FabSpi/Zone-Controller/KiCAD_libs/BC847BVN-7.step

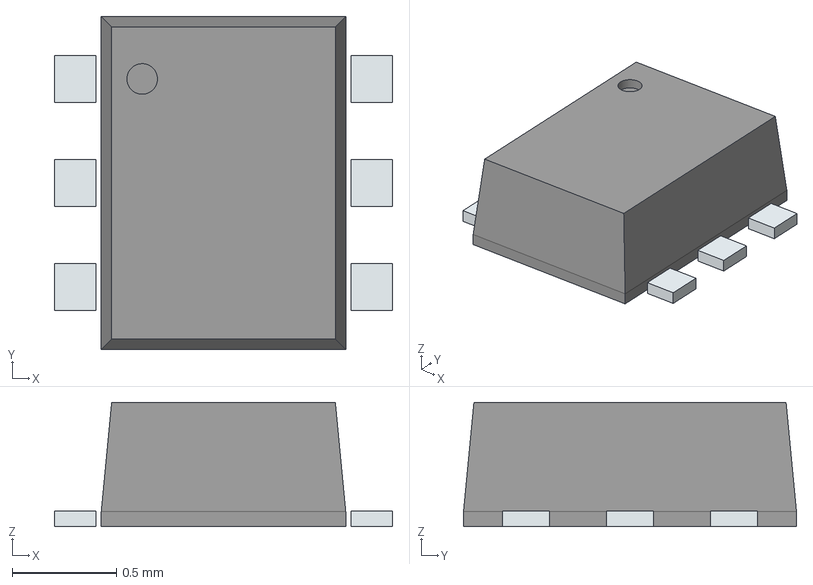
[picture p15: CAD file, 2025-10-27]
KiCAD_libs/BC847BVN-7.step
1.62 x 1.60 x 0.598 mm
PinsArrayL
PinsArrayR
