FabSpi/Zone-Controller/KiCAD_libs/TJA1022TK_118.step

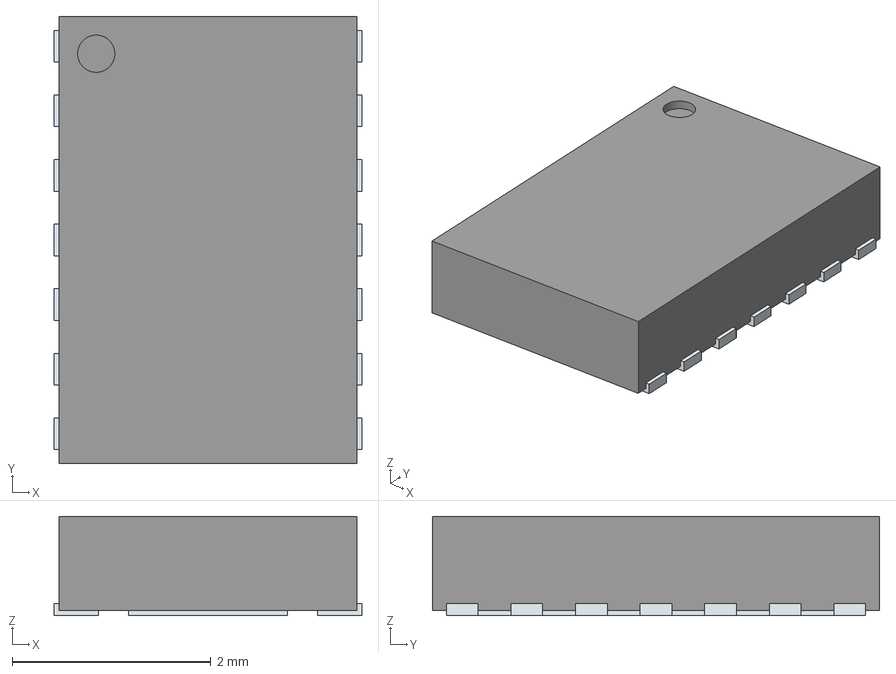
[picture p16: CAD file, 2025-10-27]
KiCAD_libs/TJA1022TK_118.step
3.10 x 4.50 x 1.00 mm
ThermalPin
PinsArrayLR
