FabSpi/Zone-Controller/KiCAD_libs/MFS2633AMBA0AD.step

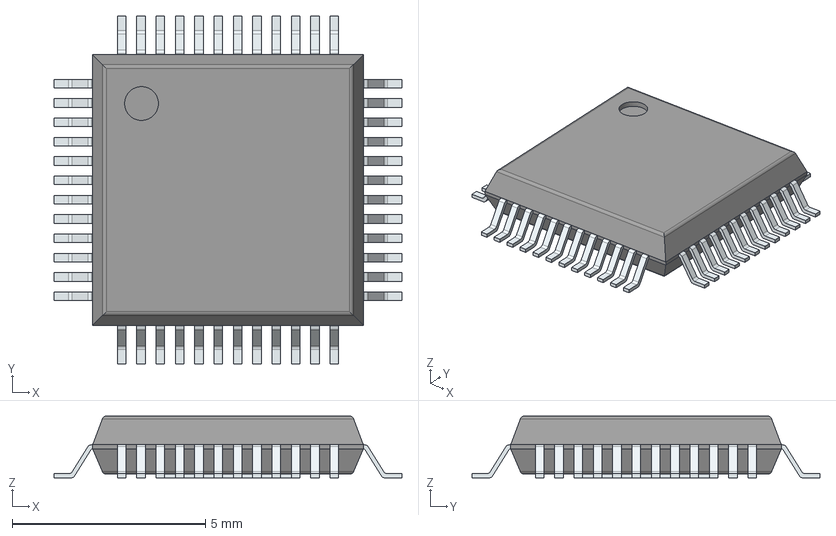
[picture p17: CAD file, 2025-10-27]
KiCAD_libs/MFS2633AMBA0AD.step
9.00 x 9.00 x 1.60 mm
PinsArrayLR
PinsArrayTB
ThermalPad
