FabSpi/Zone-Controller/KiCAD_libs/TJA1101BHN_0Z.step

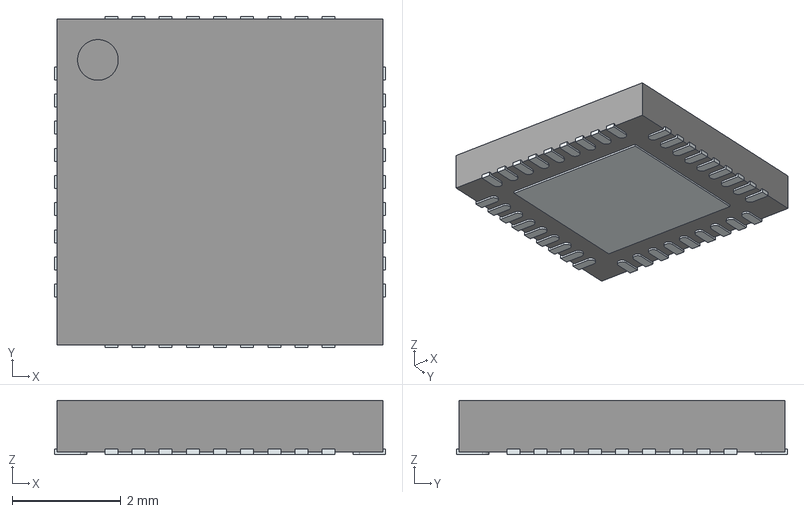
[picture p18: CAD file, 2025-10-27]
KiCAD_libs/TJA1101BHN_0Z.step
6.10 x 6.10 x 1.00 mm
ThermalPin
PinsArrayLR
PinsArrayTB
