FabSpi/Zone-Controller/KiCAD_libs/8.06.04_J-LINK_NEEDLE_ADAPTER.step

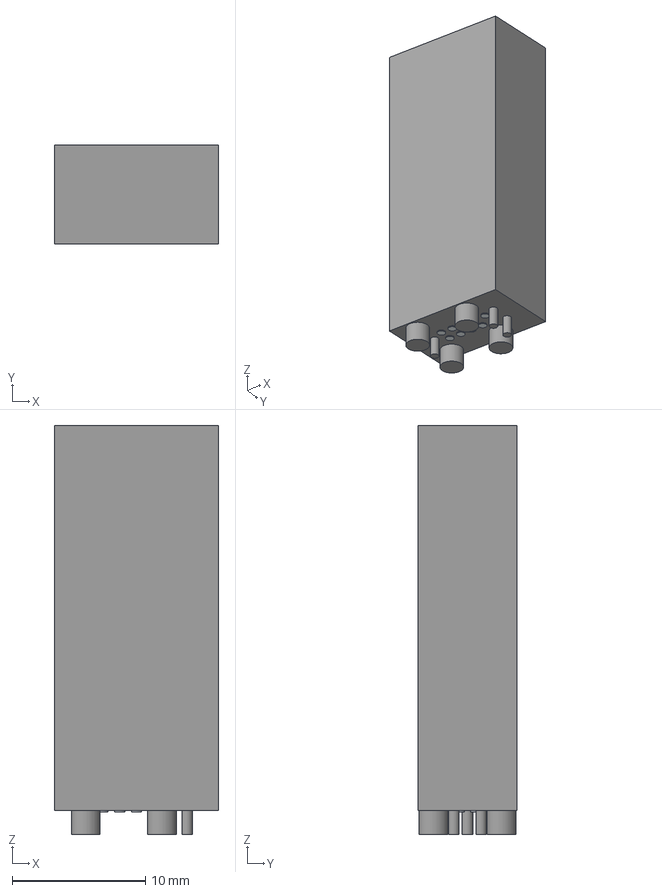
[picture p19: CAD file, 2025-10-27]
KiCAD_libs/8.06.04_J-LINK_NEEDLE_ADAPTER.step
12.3 x 7.45 x 30.7 mm
Pins
Lugs
