FabSpi/Zone-Controller/KiCAD_libs/NE555DR.step

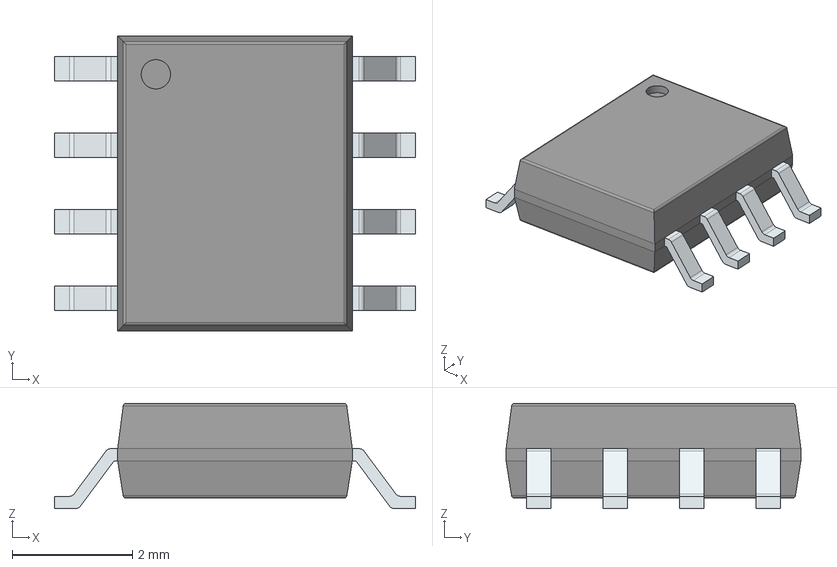
[picture p20: CAD file, 2025-10-27]
KiCAD_libs/NE555DR.step
6.00 x 4.90 x 1.75 mm
PinsArrayLR
