FabSpi/Zone-Controller/KiCAD_libs/MPLC0730L4R7.step

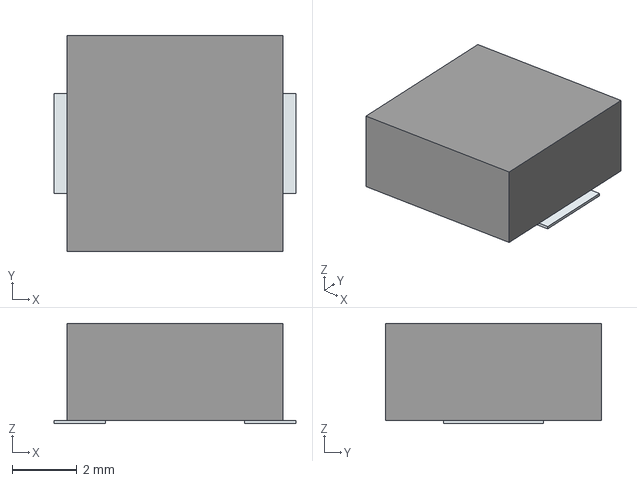
[picture p21: CAD file, 2025-10-27]
KiCAD_libs/MPLC0730L4R7.step
7.50 x 6.70 x 3.10 mm
Pins
