FabSpi/Zone-Controller/Zonencontroller/Zonencontroller.kicad_sch

## KiCad design Zonencontroller/Zonencontroller.kicad_sch (2025-10-27)

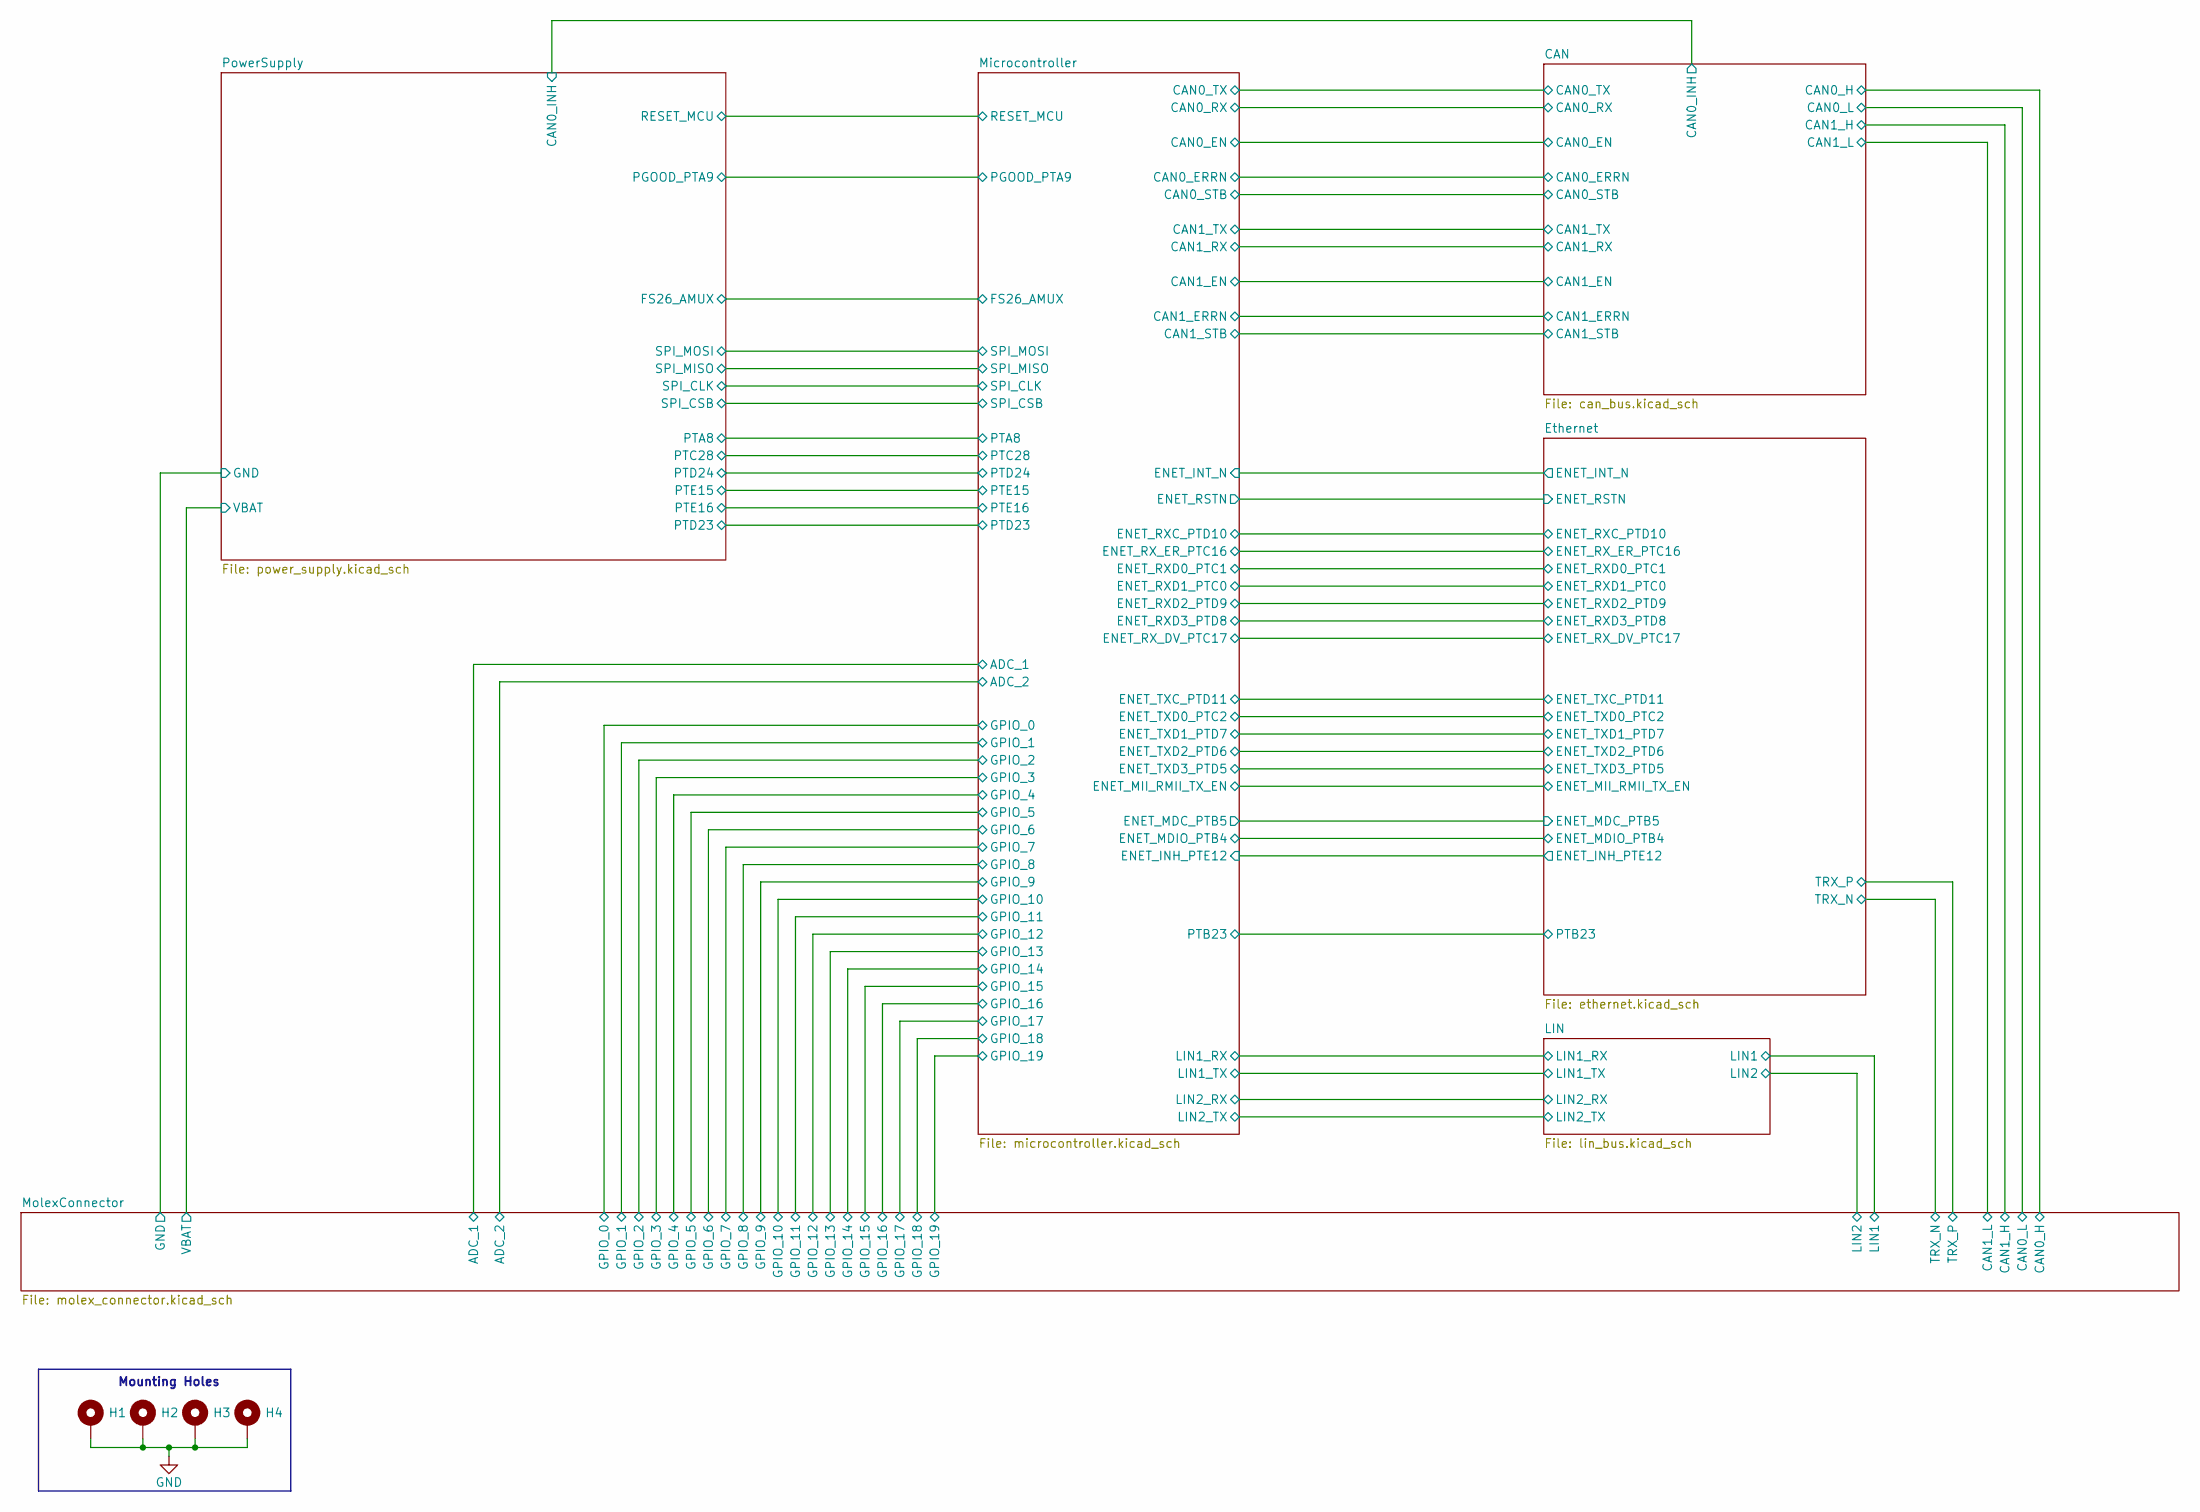
[picture p23: schematic Zonencontroller.kicad_sch]

Parts:
H1, H2, H3, H4: MountingHole_Pad; MountingHole_4.3mm_M4_DIN965_Pad_TopBottom

Connections:
GND: H1.1, H2.1, H3.1, H4.1

Notes on the sheet:
Mounting Holes
