FabSpi/Zone-Controller/Zonencontroller/can_bus.kicad_sch

## KiCad design Zonencontroller/can_bus.kicad_sch (2025-10-27)

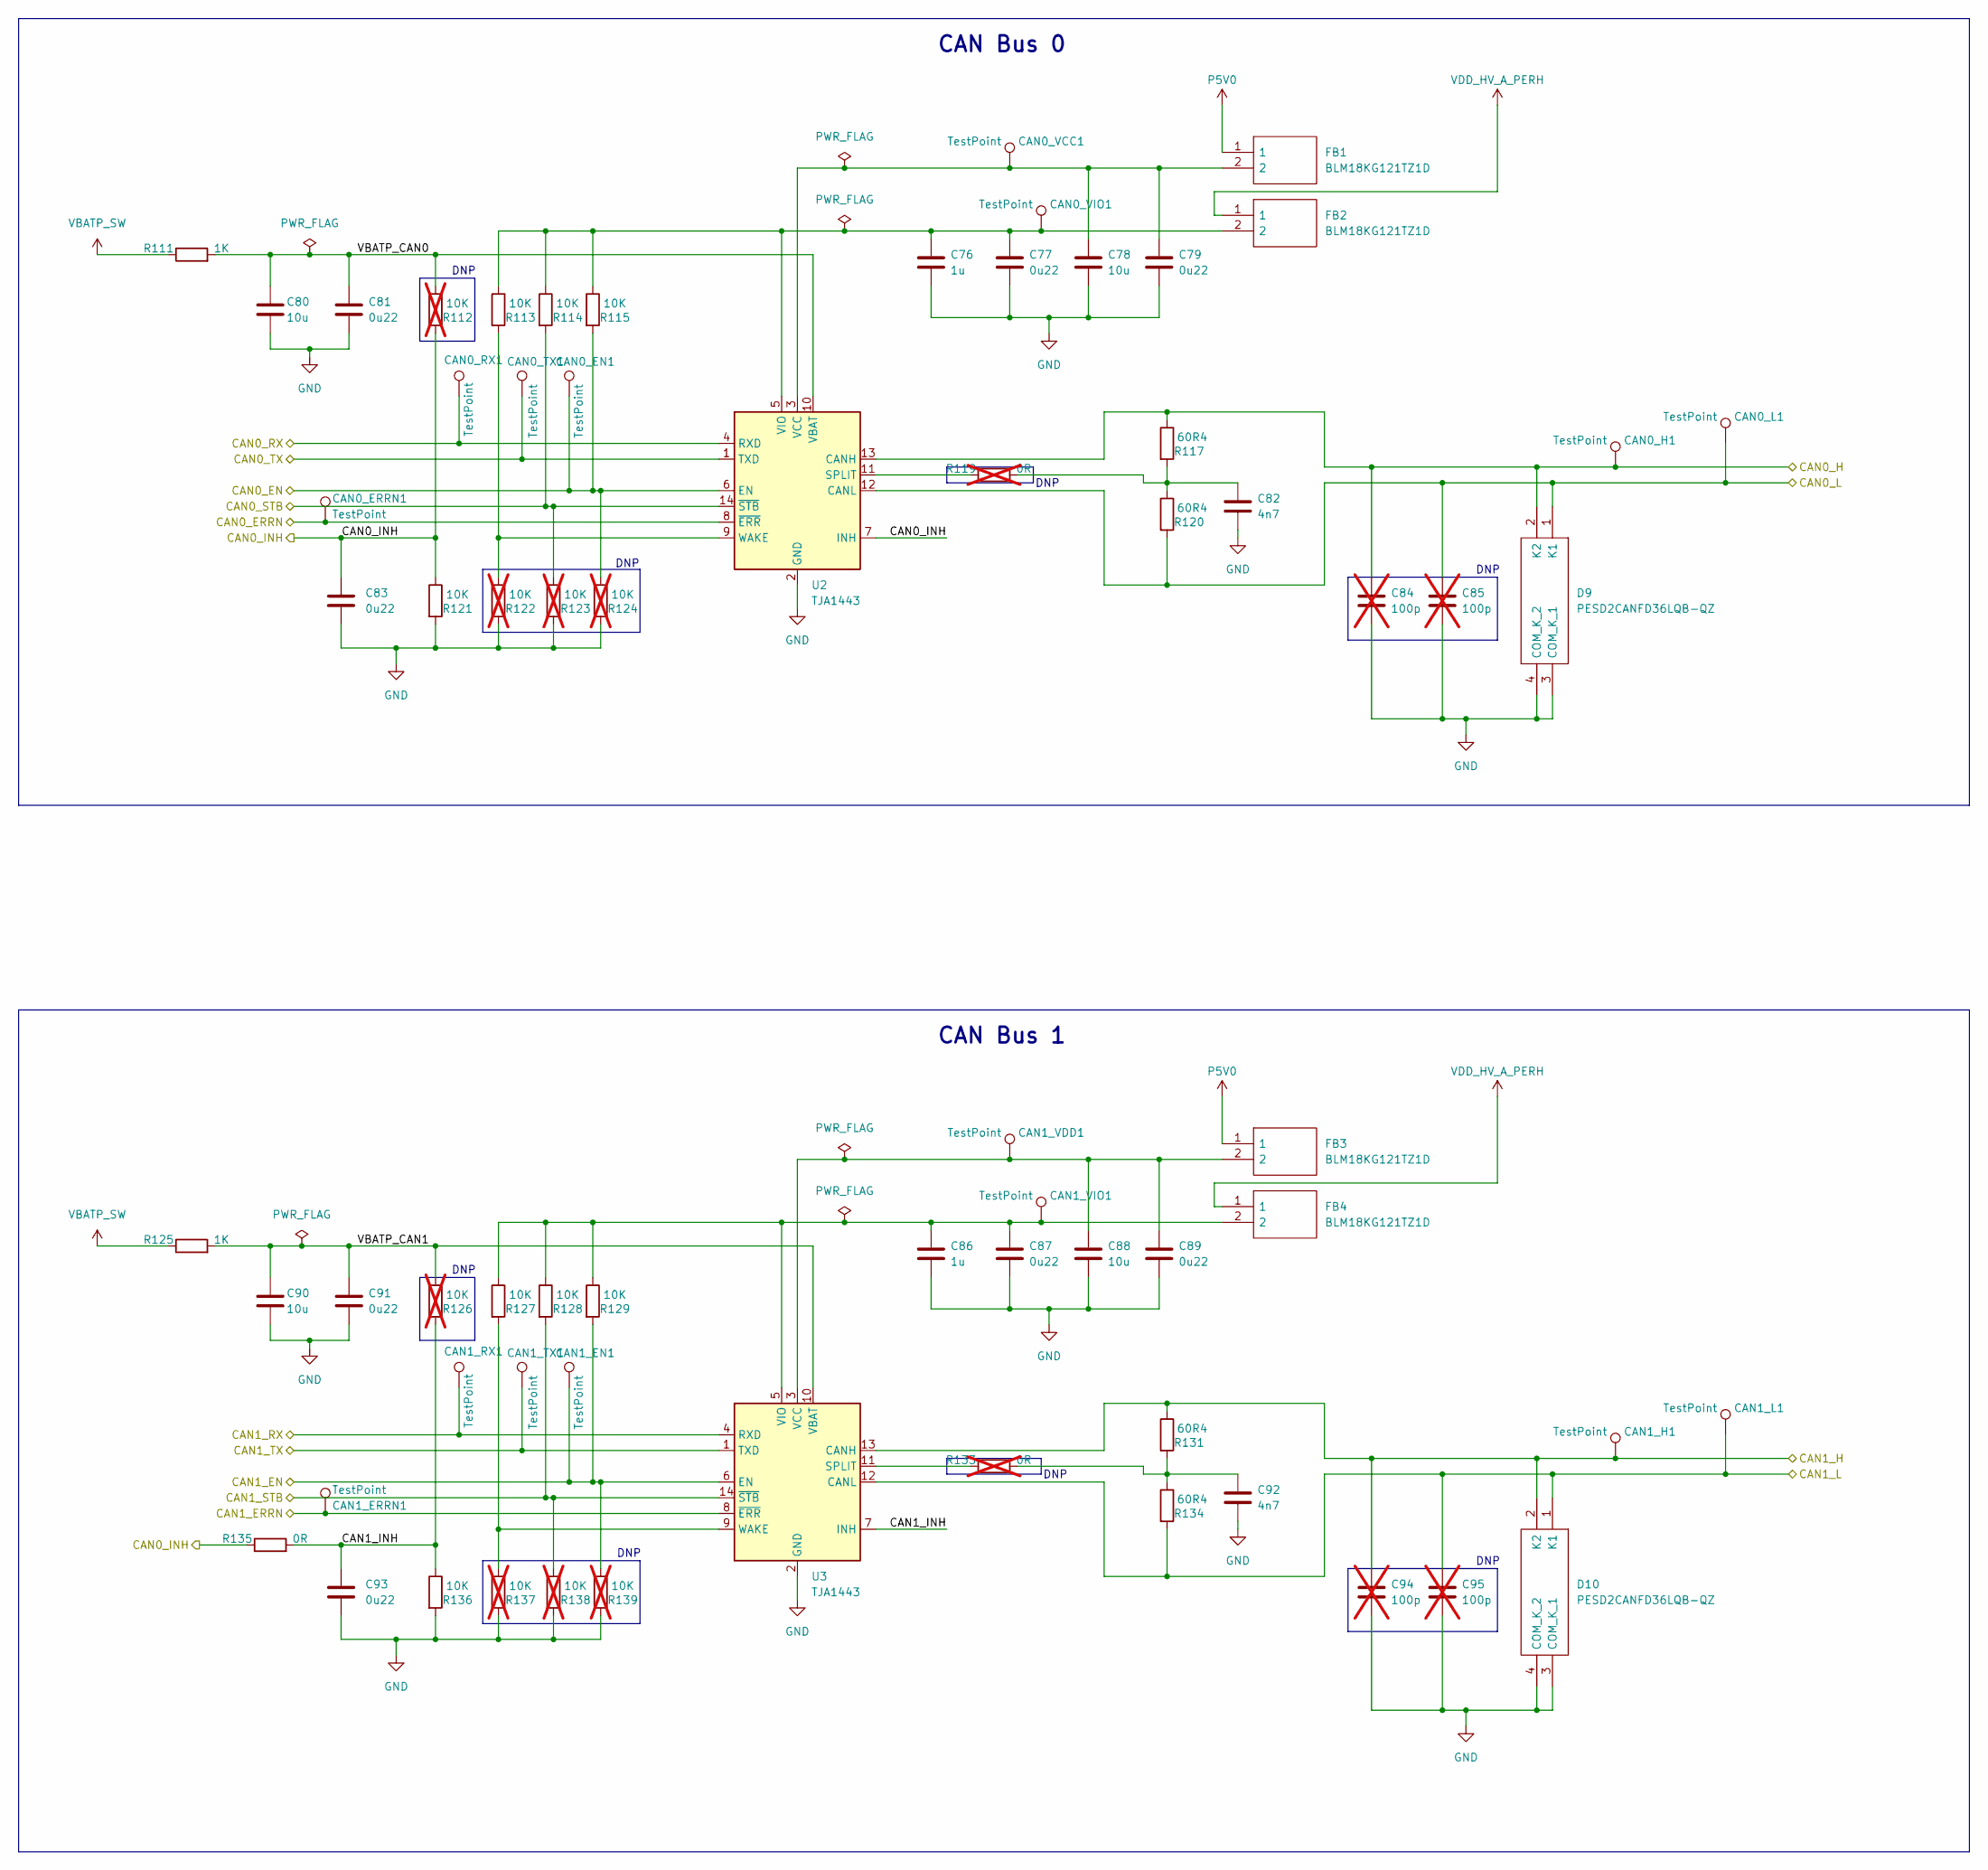
[picture p24: schematic can_bus.kicad_sch]

Parts:
C76, C86: 1u; C_0603_1608Metric
C77, C79, C81, C83, C87, C89, C91, C93: 0u22; C_0603_1608Metric
C78, C80, C88, C90: 10u; C_1206_3216Metric
C82, C92: 4n7; C_0603_1608Metric
C84, C85, C94, C95: 100p; C_0603_1608Metric; not fitted
CAN0_EN1, CAN0_ERRN1, CAN0_H1, CAN0_L1, CAN0_RX1, CAN0_TX1, CAN0_VCC1, CAN0_VIO1, CAN1_EN1, CAN1_ERRN1, CAN1_H1, CAN1_L1, CAN1_RX1, CAN1_TX1, CAN1_VDD1, CAN1_VIO1: TestPoint; TestPoint_Pad_D2.0mm
D9, D10: PESD2CANFD36LQB-QZ; PESD2CANFD36LQBQZ; Manufacturer_Part_Number PESD2CANFD36LQB-QZ; Mouser Part Number 771-PESD2CANFD3LQBQZ
FB1, FB2, FB3, FB4: BLM18KG121TZ1D; BLM18EG101TH1D; Manufacturer_Part_Number BLM18KG121TZ1D; Mouser Part Number 81-BLM18KG121TZ1D
R111, R125: 1K; R_0603_1608Metric
R112, R122, R123, R124, R126, R137, R138, R139: 10K; R_0603_1608Metric; not fitted
R113, R114, R115, R121, R127, R128, R129, R136: 10K; R_0603_1608Metric
R117, R120, R131, R134: 60R4; R_0603_1608Metric
R119, R133: 0R; R_0603_1608Metric; not fitted
R135: 0R; SolderJumper-2_P1.3mm_Bridged_Pad1.0x1.5mm
U2, U3: TJA1443; SOIC-14_3.9x8.7mm_P1.27mm

Connections:
CAN0_EN: CAN0_EN1.1, R115.2, R124.1, U2.6 (EN)
CAN0_ERRN: CAN0_ERRN1.1, U2.8 (~ERR)
CAN0_H: C84.1, CAN0_H1.1, D9.2 (K2), R117.1, U2.13 (CANH)
CAN0_INH: C83.1, R112.2, R121.1, R135.1, U2.7 (INH)
CAN0_L: C85.1, CAN0_L1.1, D9.1 (K1), R120.2, U2.12 (CANL)
CAN0_RX: CAN0_RX1.1, U2.4 (RXD)
CAN0_STB: R114.2, R123.1, U2.14 (~STB)
CAN0_TX: CAN0_TX1.1, U2.1 (TXD)
CAN1_EN: CAN1_EN1.1, R129.2, R139.1, U3.6 (EN)
CAN1_ERRN: CAN1_ERRN1.1, U3.8 (~ERR)
CAN1_H: C94.1, CAN1_H1.1, D10.2 (K2), R131.1, U3.13 (CANH)
CAN1_INH: C93.1, R126.2, R135.2, R136.1, U3.7 (INH)
CAN1_L: C95.1, CAN1_L1.1, D10.1 (K1), R134.2, U3.12 (CANL)
CAN1_RX: CAN1_RX1.1, U3.4 (RXD)
CAN1_STB: R128.2, R138.1, U3.14 (~STB)
CAN1_TX: CAN1_TX1.1, U3.1 (TXD)
GND: C76.2, C77.2, C78.2, C79.2, C80.2, C81.2, C82.2, C83.2, C84.2, C85.2, C86.2, C87.2, C88.2, C89.2, C90.2, C91.2, C92.2, C93.2, C94.2, C95.2, D9.3 (COM_K_1), D9.4 (COM_K_2), D10.3 (COM_K_1), D10.4 (COM_K_2), R121.2, R122.2, R123.2, R124.2, R136.2, R137.2, R138.2, R139.2, U2.2 (GND), U3.2 (GND)
unnamed: C76.1, C77.1, CAN0_VIO1.1, FB2.2, R113.1, R114.1, R115.1, U2.5 (VIO)
unnamed: C78.1, C79.1, CAN0_VCC1.1, FB1.2, U2.3 (VCC)
unnamed: C82.1, R117.2, R119.2, R120.1
unnamed: C86.1, C87.1, CAN1_VIO1.1, FB4.2, R127.1, R128.1, R129.1, U3.5 (VIO)
unnamed: C88.1, C89.1, CAN1_VDD1.1, FB3.2, U3.3 (VCC)
unnamed: C92.1, R131.2, R133.2, R134.1
unnamed: R113.2, R122.1, U2.9 (WAKE)
unnamed: R119.1, U2.11 (SPLIT)
unnamed: R127.2, R137.1, U3.9 (WAKE)
unnamed: R133.1, U3.11 (SPLIT)
P5V0: FB1.1, FB3.1
VBATP_CAN0: C80.1, C81.1, R111.2, R112.1, U2.10 (VBAT)
VBATP_CAN1: C90.1, C91.1, R125.2, R126.1, U3.10 (VBAT)
VBATP_SW: R111.1, R125.1
VDD_HV_A_PERH: FB2.1, FB4.1

Notes on the sheet:
DNP
CAN Bus 0
CAN Bus 1
