FabSpi/Zone-Controller/Zonencontroller/ethernet.kicad_sch

## KiCad design Zonencontroller/ethernet.kicad_sch (2025-10-27)

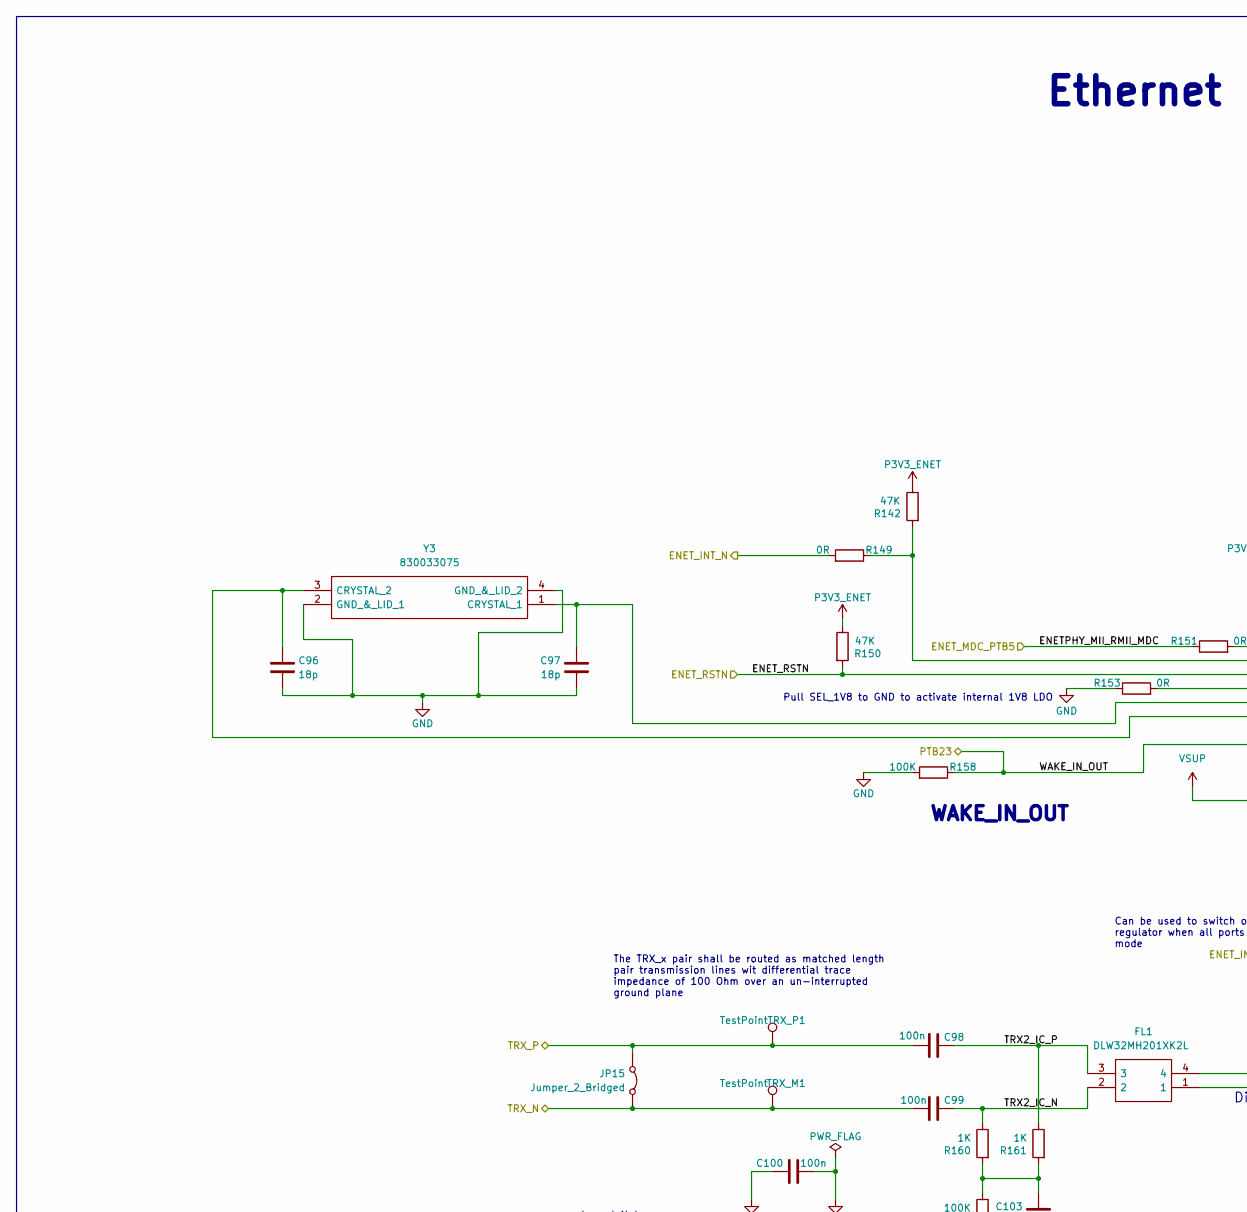
[picture p25: schematic ethernet.kicad_sch, part in row 1, column 1]

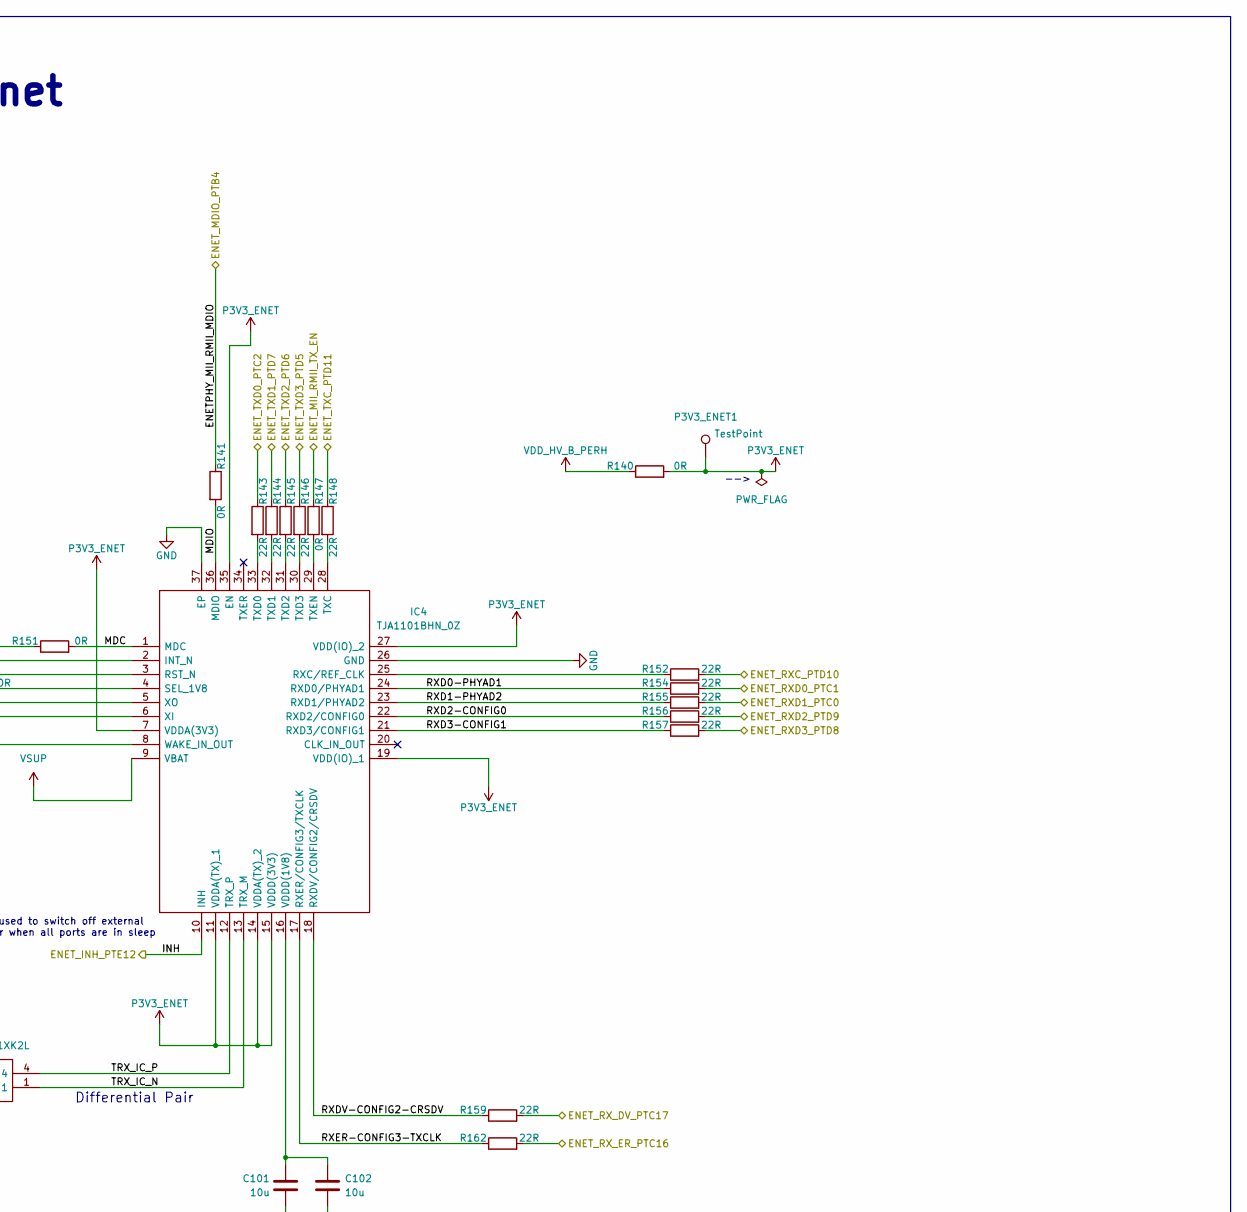
[picture p26: schematic ethernet.kicad_sch, part in row 1, column 2]

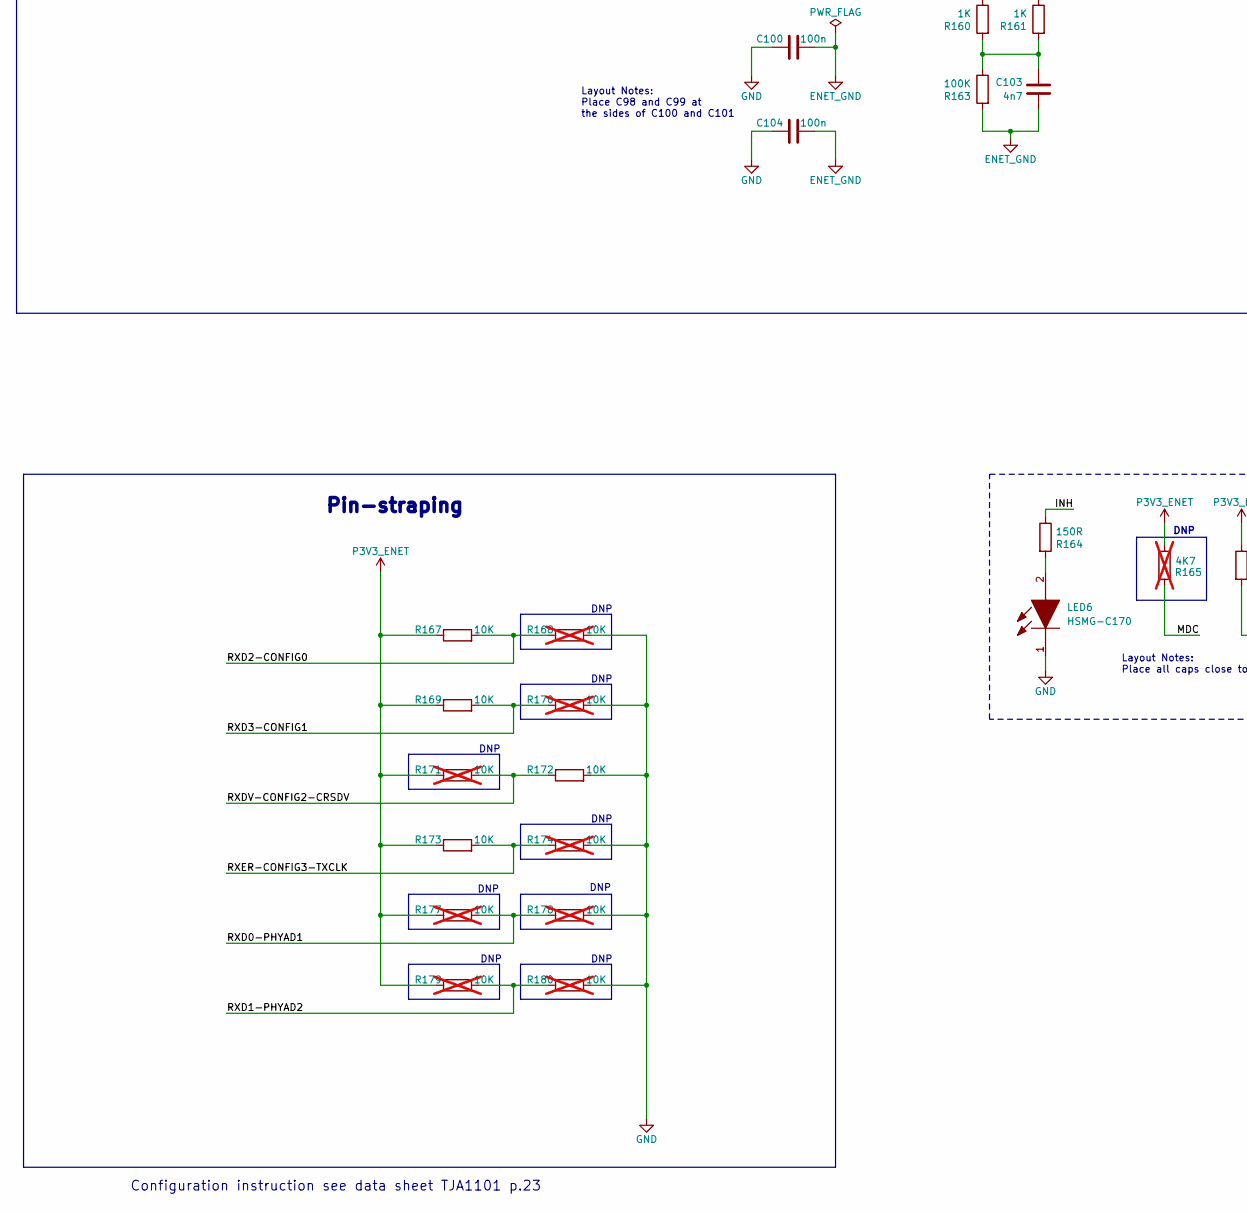
[picture p27: schematic ethernet.kicad_sch, part in row 2, column 1]

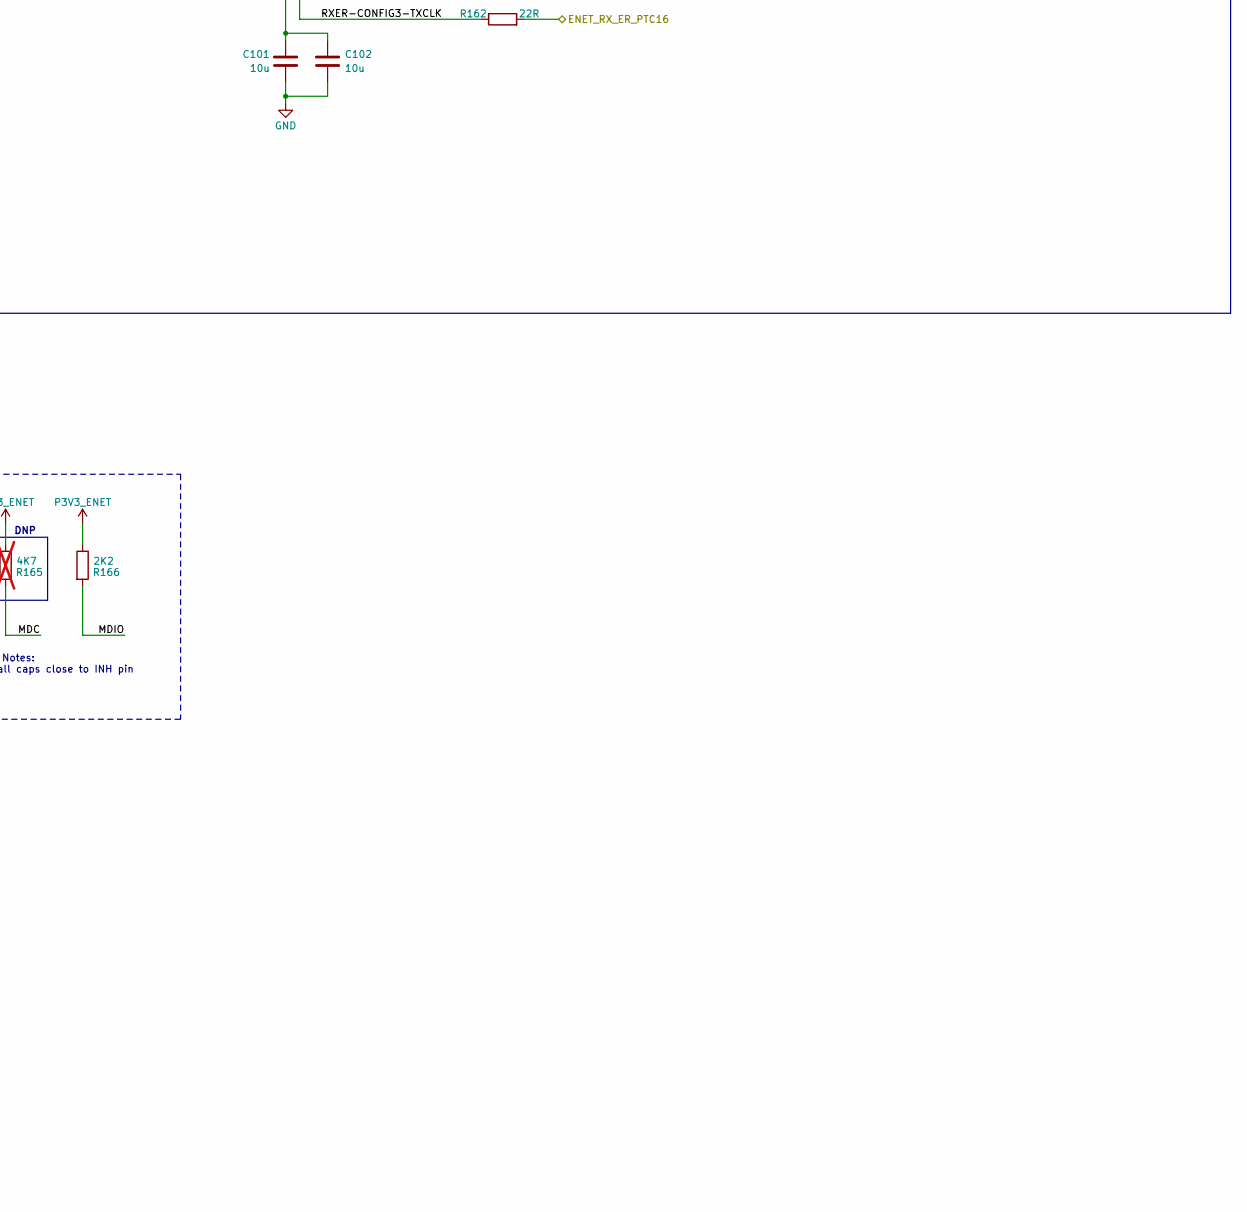
[picture p28: schematic ethernet.kicad_sch, part in row 2, column 2]

Parts:
C96, C97: 18p; C_0603_1608Metric
C98, C99, C100, C104: 100n; C_0603_1608Metric
C101, C102: 10u; C_1206_3216Metric
C103: 4n7; C_0603_1608Metric
FL1: DLW32MH201XK2L; DLW32MH101XK2L; Manufacturer_Part_Number DLW32MH201XK2L; Mouser Part Number 81-DLW32MH201XK2L
IC4: TJA1101BHN_0Z; QFN50P600X600X100-37N-D; Manufacturer_Part_Number TJA1101BHN/0Z; Mouser Part Number 771-TJA1101BHN/0Z
JP15: Jumper_2_Bridged; PinHeader_1x02_P2.54mm_Vertical
LED6: HSMG-C170; LEDC2012X80N; Manufacturer_Part_Number HSMG-C170; Mouser Part Number 630-HSMG-C170
P3V3_ENET1: TestPoint; TestPoint_Pad_D2.0mm
R140, R141, R147, R149, R151, R153: 0R; SolderJumper-2_P1.3mm_Bridged_Pad1.0x1.5mm
R142, R150: 47K; R_0603_1608Metric
R143, R144, R145, R146, R148, R152, R154, R155, R156, R157, R159, R162: 22R; R_0603_1608Metric
R158, R163: 100K; R_0603_1608Metric
R160, R161: 1K; R_0603_1608Metric
R164: 150R; R_0603_1608Metric
R165: 4K7; R_0603_1608Metric; not fitted
R166: 2K2; R_0603_1608Metric
R167, R169, R172, R173: 10K; R_0603_1608Metric
R168, R170, R171, R174, R177, R178, R179, R180: 10K; R_0603_1608Metric; not fitted
TRX_M1: TestPoint; TestPoint_Pad_D2.0mm
TRX_P1: TestPoint; TestPoint_Pad_D2.0mm
Y3: 830033075; Manufacturer_Part_Number 830033075; Mouser Part Number 710-830033075

Connections:
ENET_GND: C100.2, C103.2, C104.2, R163.2
ENET_INH_PTE12: IC4.10 (INH), R164.1
ENET_INT_N: R149.2
ENET_MDC_PTB5: R151.1
ENET_MDIO_PTB4: R141.1
ENET_MII_RMII_TX_EN: R147.1
ENET_RSTN: IC4.3 (RST_N), R150.2
ENET_RXC_PTD10: R152.2
ENET_RXD0_PTC1: R154.2
ENET_RXD1_PTC0: R155.2
ENET_RXD2_PTD9: R156.2
ENET_RXD3_PTD8: R157.2
ENET_RX_DV_PTC17: R159.2
ENET_RX_ER_PTC16: R162.2
ENET_TXC_PTD11: R148.1
ENET_TXD0_PTC2: R143.1
ENET_TXD1_PTD7: R144.1
ENET_TXD2_PTD6: R145.1
ENET_TXD3_PTD5: R146.1
GND: C96.2, C97.2, C100.1, C101.2, C102.2, C104.1, IC4.26 (GND), IC4.37 (EP), LED6.1, R153.1, R158.2, R168.2, R170.2, R172.2, R174.2, R178.2, R180.2, Y3.2 (GND_&_LID_1), Y3.4 (GND_&_LID_2)
MDC: IC4.1 (MDC), R151.2, R165.2
MDIO: IC4.36 (MDIO), R141.2, R166.2
unnamed: C96.1, IC4.6 (XI), Y3.3 (CRYSTAL_2)
unnamed: C97.1, IC4.5 (XO), Y3.1 (CRYSTAL_1)
unnamed: C101.1, C102.1, IC4.16 (VDDD(1V8))
unnamed: C103.1, R160.2, R161.2, R163.1
unnamed: IC4.2 (INT_N), R142.2, R149.1
unnamed: IC4.4 (SEL_1V8), R153.2
unnamed: IC4.25 (RXC/REF_CLK), R152.1
unnamed: IC4.28 (TXC), R148.2
unnamed: IC4.29 (TXEN), R147.2
unnamed: IC4.30 (TXD3), R146.2
unnamed: IC4.31 (TXD2), R145.2
unnamed: IC4.32 (TXD1), R144.2
unnamed: IC4.33 (TXD0), R143.2
unnamed: LED6.2, R164.2
P3V3_ENET: IC4.7 (VDDA(3V3)), IC4.11 (VDDA(TX)_1), IC4.14 (VDDA(TX)_2), IC4.15 (VDDD(3V3)), IC4.19 (VDD(IO)_1), IC4.27 (VDD(IO)_2), IC4.35 (EN), P3V3_ENET1.1, R140.2, R142.1, R150.1, R165.1, R166.1, R167.1, R169.1, R171.1, R173.1, R177.1, R179.1
PTB23: IC4.8 (WAKE_IN_OUT), R158.1
RXD0-PHYAD1: IC4.24 (RXD0/PHYAD1), R154.1, R177.2, R178.1
RXD1-PHYAD2: IC4.23 (RXD1/PHYAD2), R155.1, R179.2, R180.1
RXD2-CONFIG0: IC4.22 (RXD2/CONFIG0), R156.1, R167.2, R168.1
RXD3-CONFIG1: IC4.21 (RXD3/CONFIG1), R157.1, R169.2, R170.1
RXDV-CONFIG2-CRSDV: IC4.18 (RXDV/CONFIG2/CRSDV), R159.1, R171.2, R172.1
RXER-CONFIG3-TXCLK: IC4.17 (RXER/CONFIG3/TXCLK), R162.1, R173.2, R174.1
TRX2_IC_N: C99.1, FL1.2, R160.1
TRX2_IC_P: C98.1, FL1.3, R161.1
TRX_IC_N: FL1.1, IC4.13 (TRX_M)
TRX_IC_P: FL1.4, IC4.12 (TRX_P)
TRX_N: C99.2, JP15.1 (A), TRX_M1.1
TRX_P: C98.2, JP15.2 (B), TRX_P1.1
VDD_HV_B_PERH: R140.1
VSUP: IC4.9 (VBAT)

Notes on the sheet:
Configuration instruction see data sheet TJA1101 p.23
The TRX_x pair shall be routed as matched length pair transmission lines wit differential trace impedance of 100 Ohm over an un-interrupted ground plane
WAKE_IN_OUT
DNP
-->
Differential Pair
Ethernet
Layout Notes: Place all caps close to INH pin
Pin-straping
Can be used to switch off external regulator when all ports are in sleep mode
Pull SEL_1V8 to GND to activate internal 1V8 LDO
Layout Notes: Place C98 and C99 at the sides of C100 and C101
