FabSpi/Zone-Controller/Zonencontroller/lin_bus.kicad_sch

## KiCad design Zonencontroller/lin_bus.kicad_sch (2025-10-27)

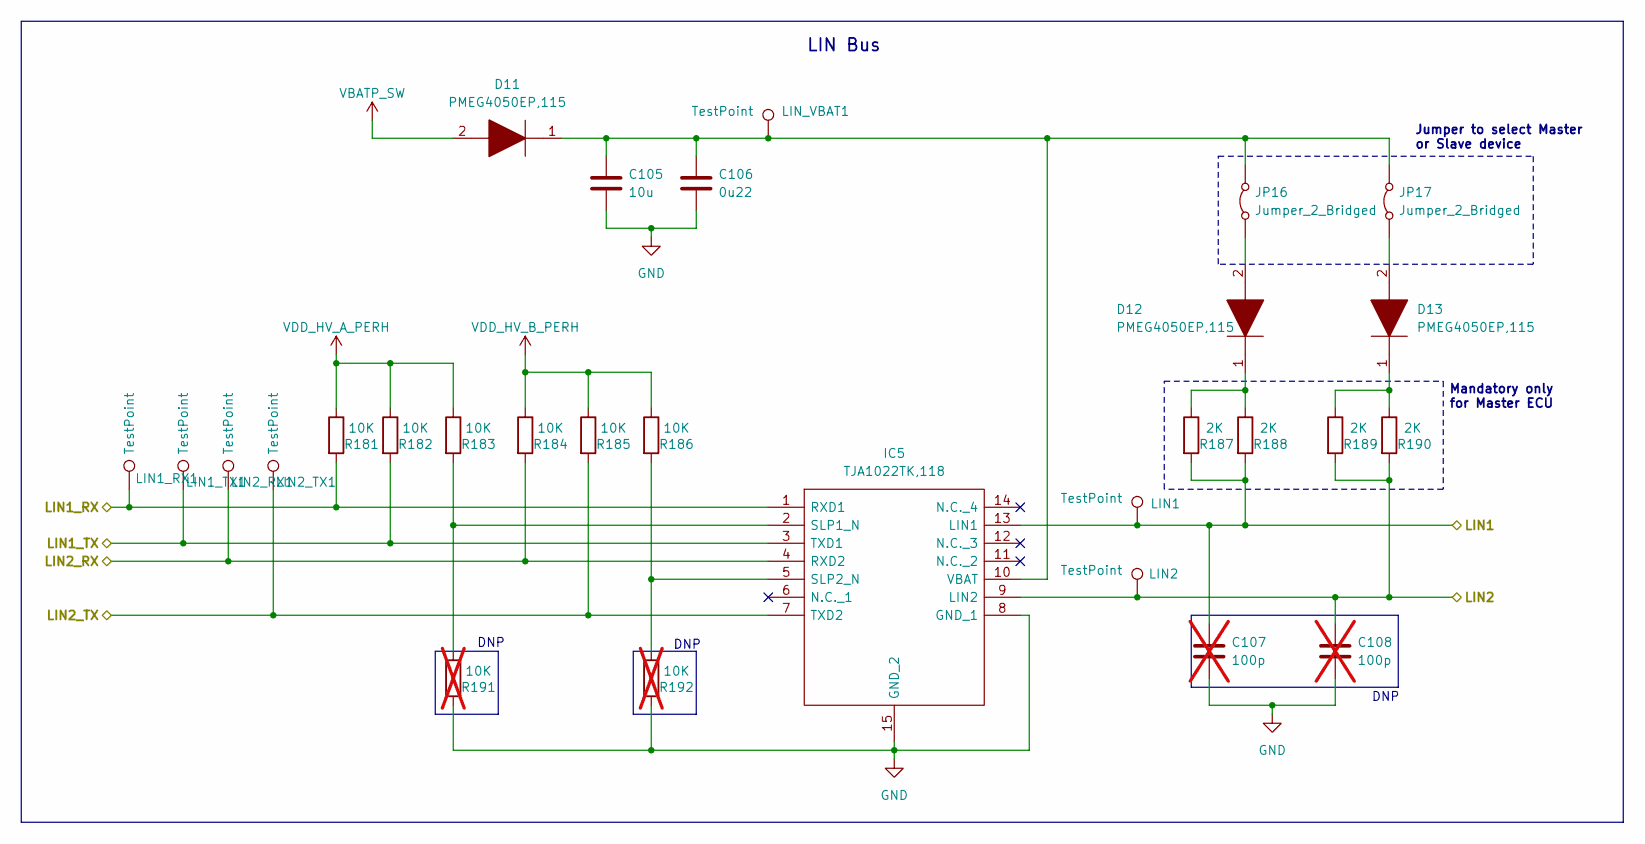
[picture p29: schematic lin_bus.kicad_sch]

Parts:
C105: 10u; C_1206_3216Metric
C106: 0u22; C_0603_1608Metric
C107, C108: 100p; C_0603_1608Metric; not fitted
D11, D12, D13: PMEG4050EP,115; SODFL4725X110N; Manufacturer_Part_Number PMEG4050EP,115; Mouser Part Number 771-PMEG4050EP115
IC5: TJA1022TK,118; SON65P300X450X100-15N; Manufacturer_Part_Number TJA1022TK,118; Mouser Part Number 771-TJA1022TK118
JP16, JP17: Jumper_2_Bridged; PinHeader_1x02_P2.54mm_Vertical
LIN1, LIN1_RX1, LIN1_TX1, LIN2, LIN2_RX1, LIN2_TX1: TestPoint; TestPoint_Pad_D2.0mm
LIN_VBAT1: TestPoint; TestPoint_Pad_D2.0mm
R181, R182, R183, R184, R185, R186: 10K; R_0603_1608Metric
R187, R188, R189, R190: 2K; R_0603_1608Metric
R191, R192: 10K; R_0603_1608Metric; not fitted

Connections:
GND: C105.2, C106.2, C107.2, C108.2, IC5.8 (GND_1), IC5.15 (GND_2), R191.2, R192.2
LIN1: C107.1, IC5.13 (LIN1), LIN1.1, R187.2, R188.2
LIN1_RX: IC5.1 (RXD1), LIN1_RX1.1, R181.2
LIN1_TX: IC5.3 (TXD1), LIN1_TX1.1, R182.2
LIN2: C108.1, IC5.9 (LIN2), LIN2.1, R189.2, R190.2
LIN2_RX: IC5.4 (RXD2), LIN2_RX1.1, R184.2
LIN2_TX: IC5.7 (TXD2), LIN2_TX1.1, R185.2
unnamed: C105.1, C106.1, D11.1, IC5.10 (VBAT), JP16.2 (B), JP17.2 (B), LIN_VBAT1.1
unnamed: D12.1, R187.1, R188.1
unnamed: D12.2, JP16.1 (A)
unnamed: D13.1, R189.1, R190.1
unnamed: D13.2, JP17.1 (A)
unnamed: IC5.2 (SLP1_N), R183.2, R191.1
unnamed: IC5.5 (SLP2_N), R186.2, R192.1
VBATP_SW: D11.2
VDD_HV_A_PERH: R181.1, R182.1, R183.1
VDD_HV_B_PERH: R184.1, R185.1, R186.1

Notes on the sheet:
DNP
Mandatory only for Master ECU
Jumper to select Master or Slave device
LIN Bus
