FabSpi/Zone-Controller/Zonencontroller/microcontroller.kicad_sch

## KiCad design Zonencontroller/microcontroller.kicad_sch (2025-10-27)

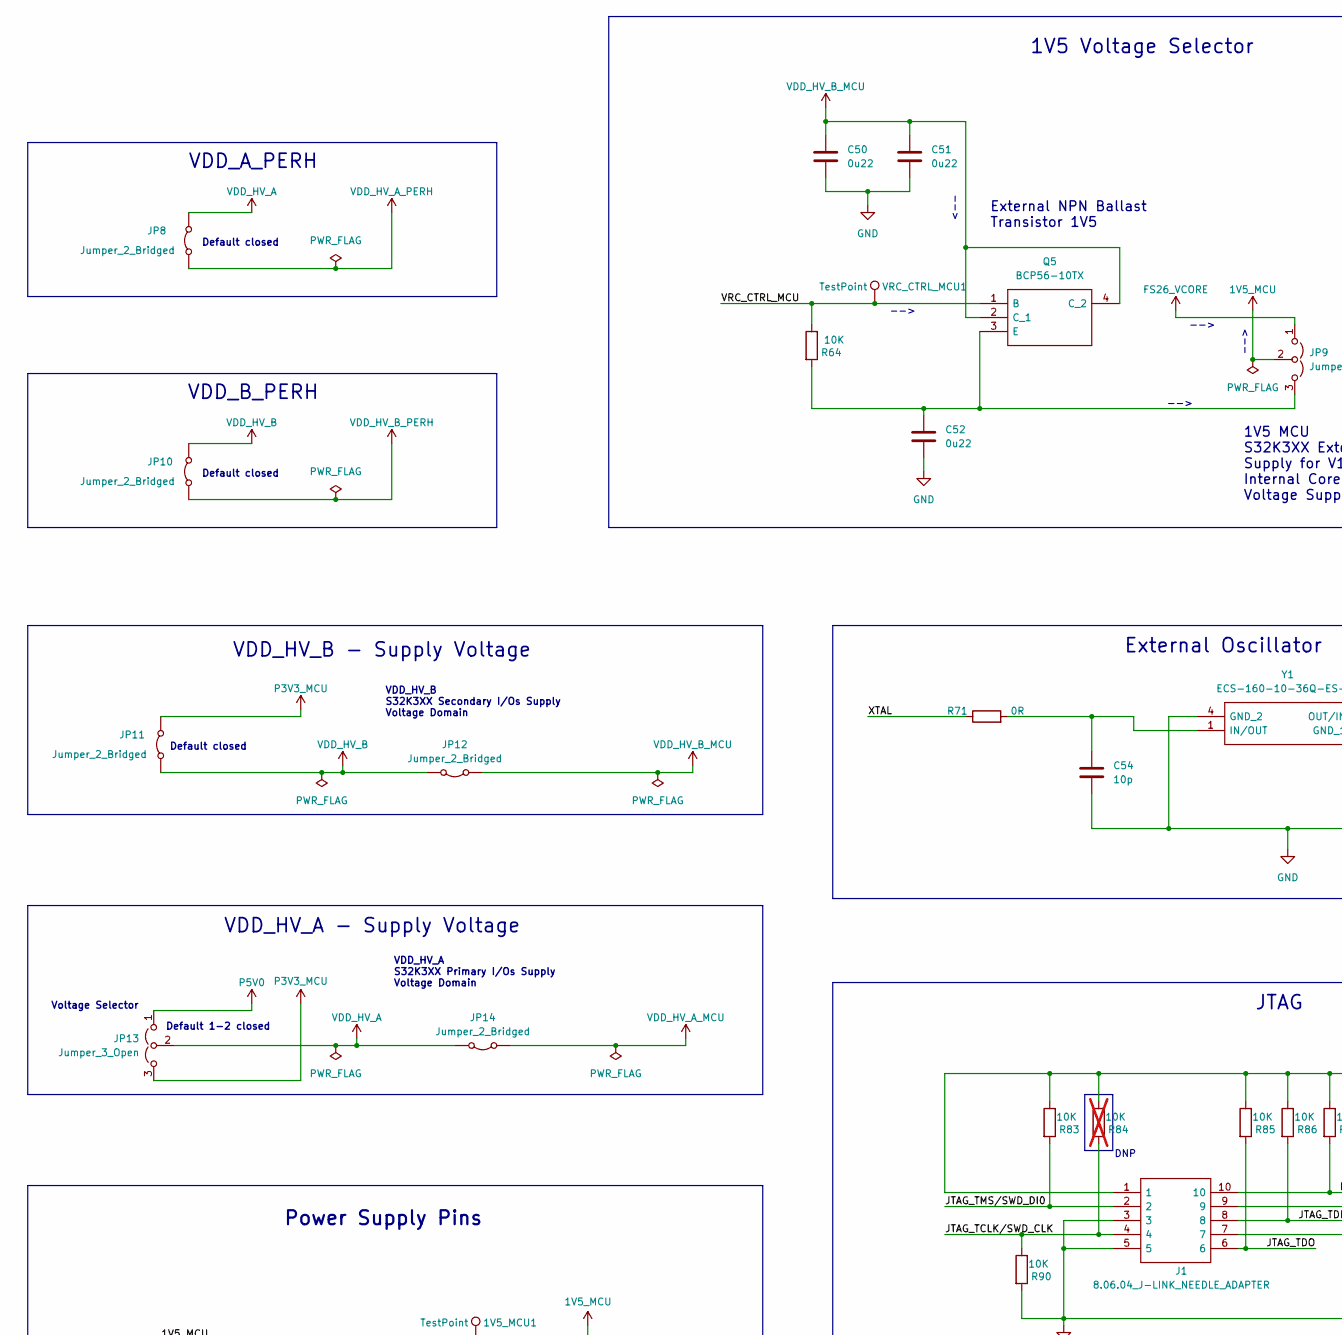
[picture p30: schematic microcontroller.kicad_sch, part in row 1, column 1]

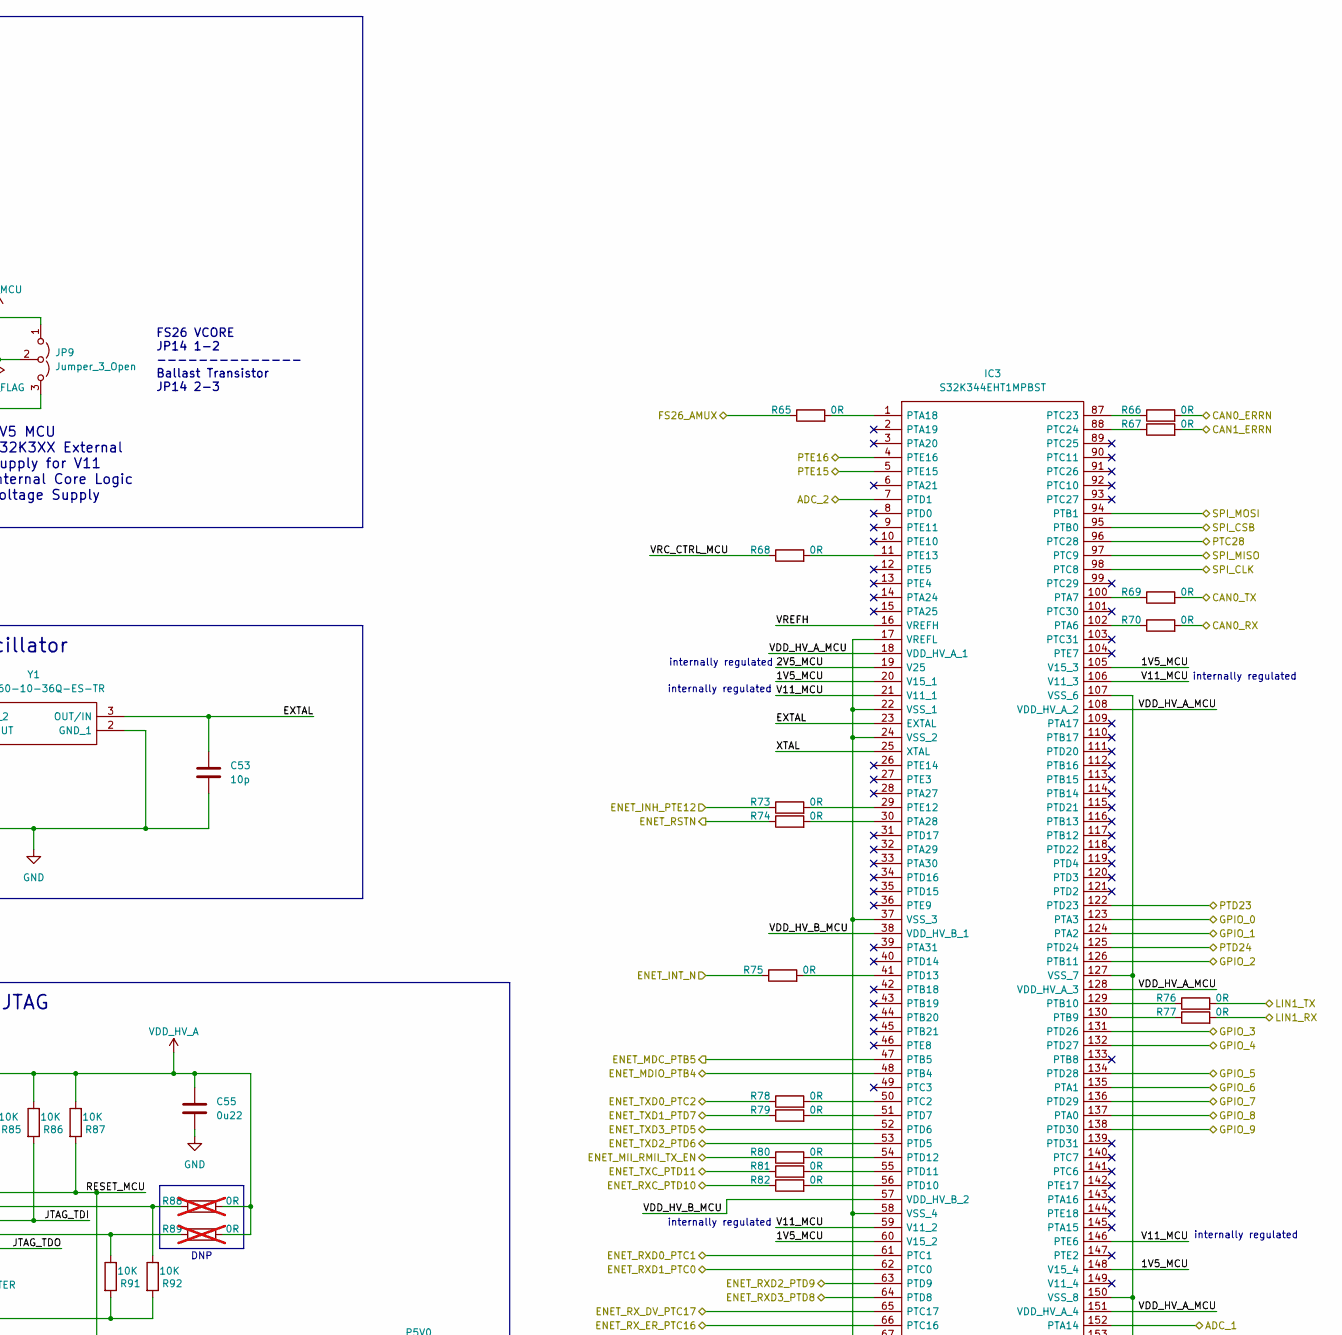
[picture p31: schematic microcontroller.kicad_sch, part in row 1, column 2]

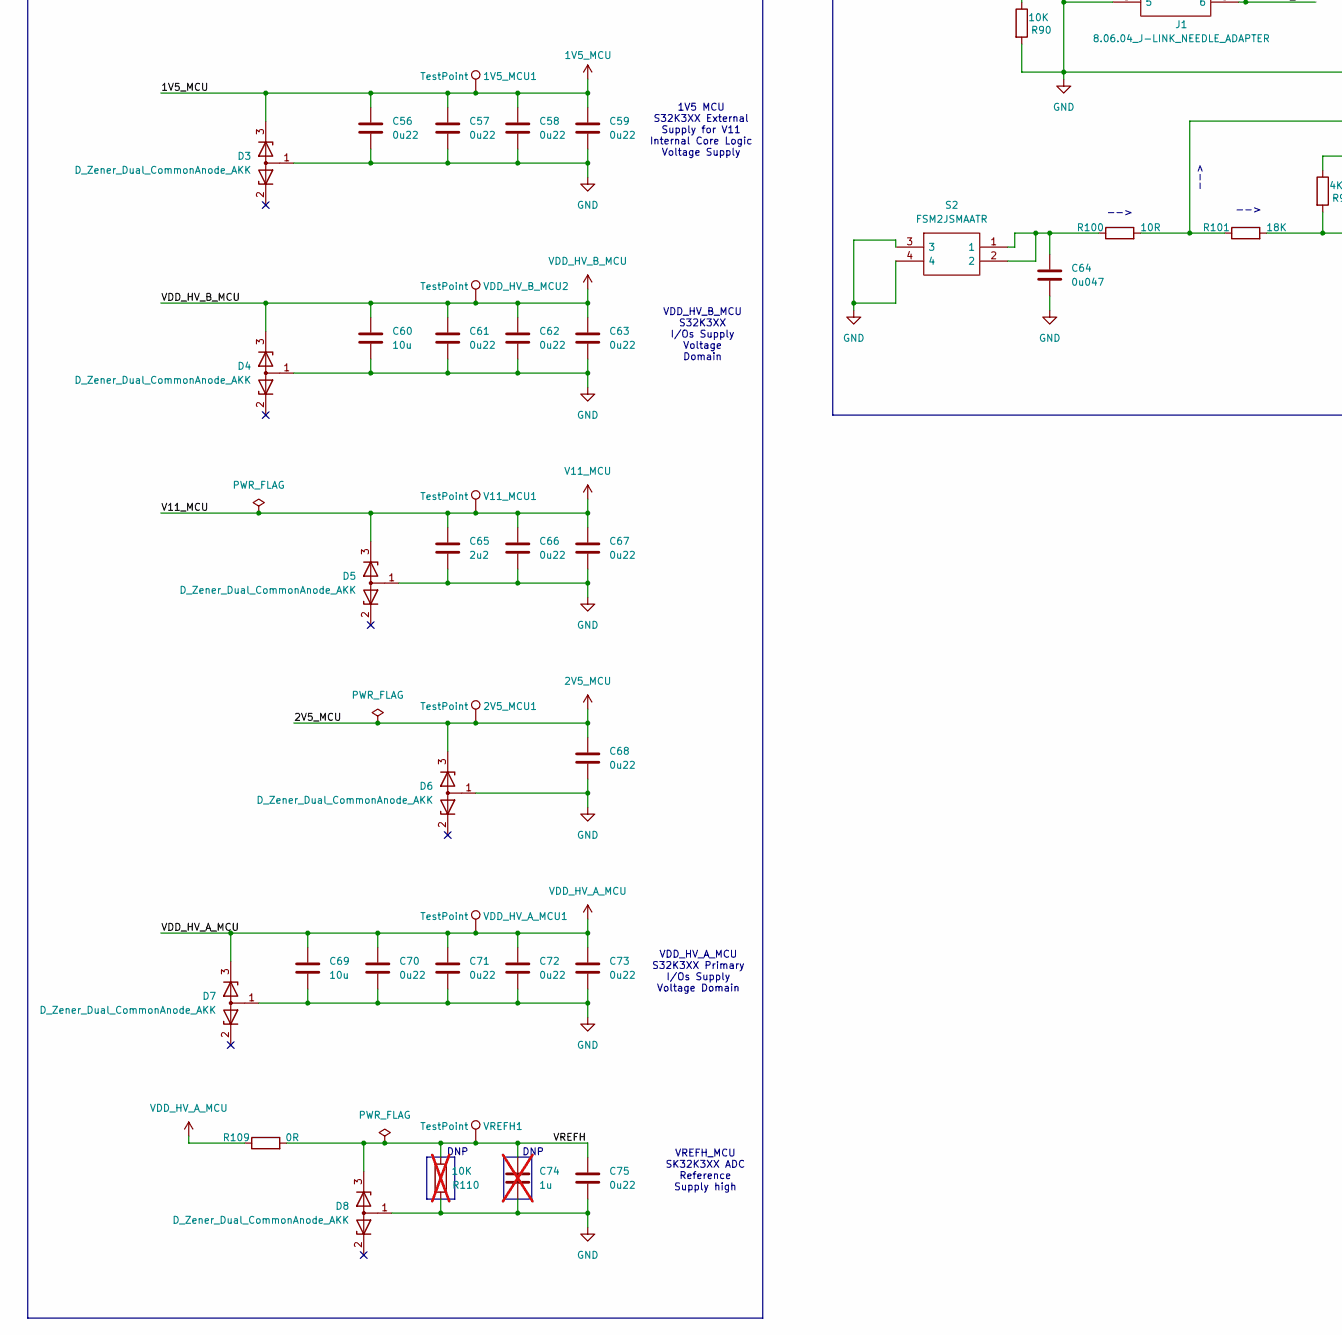
[picture p32: schematic microcontroller.kicad_sch, part in row 2, column 1]

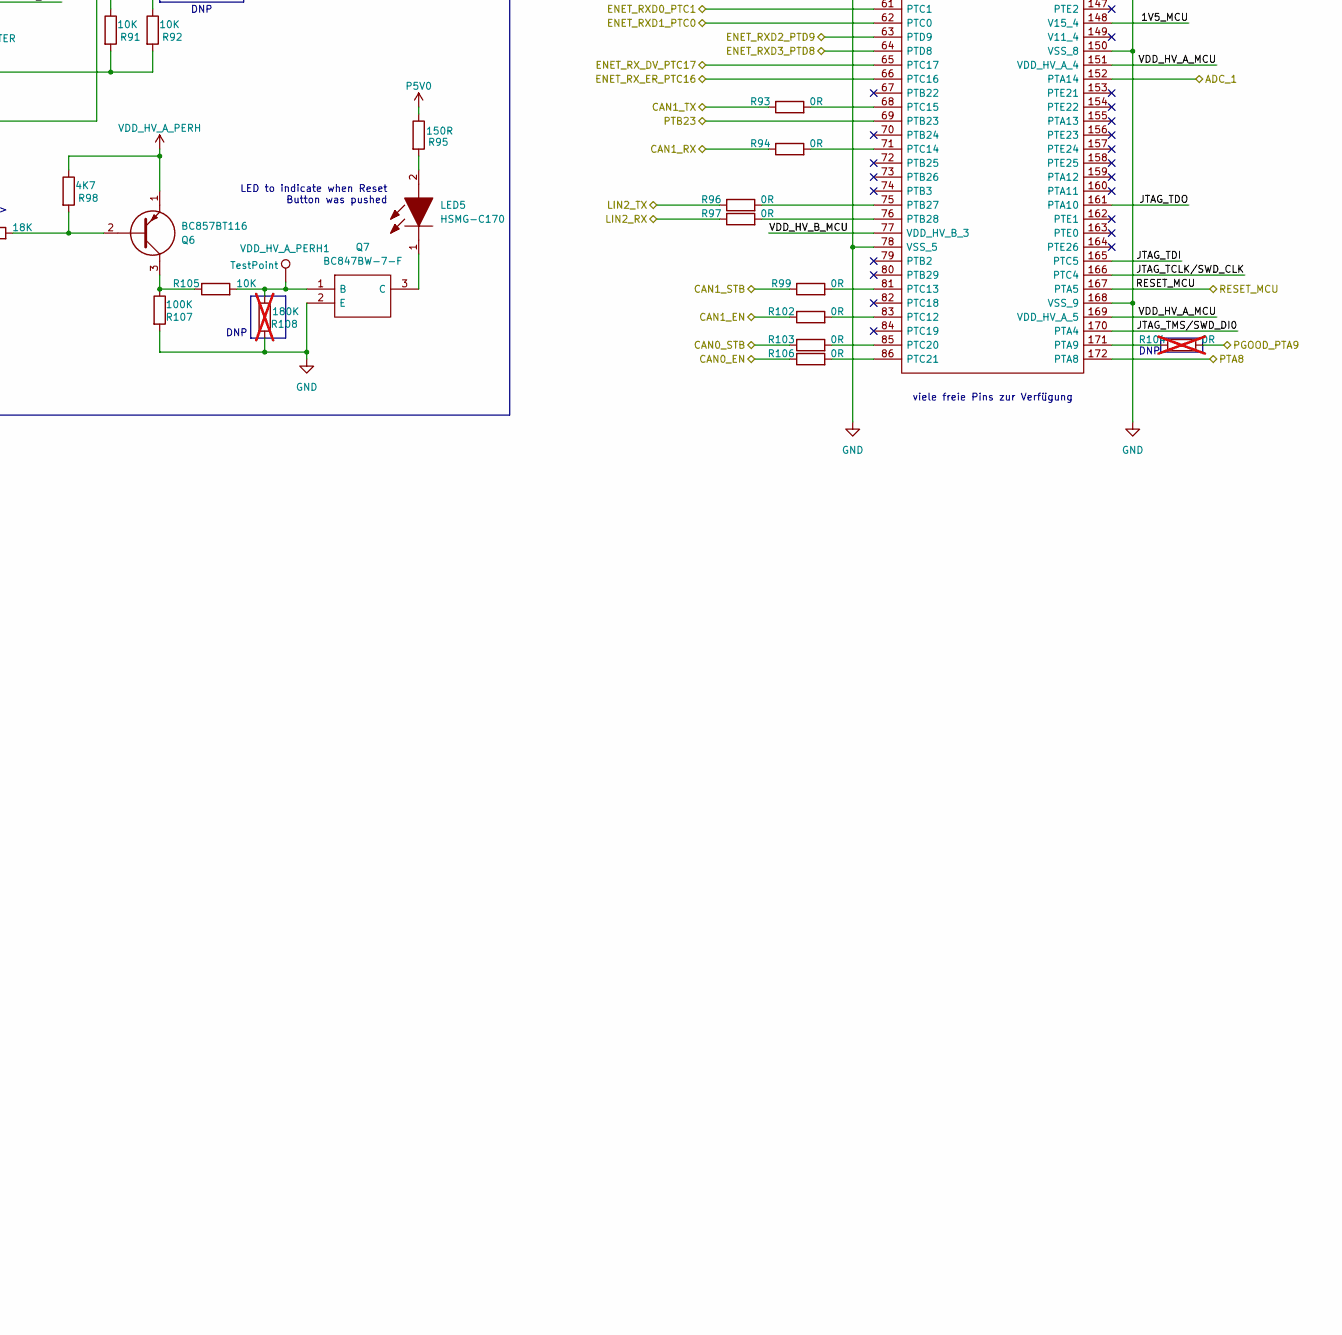
[picture p33: schematic microcontroller.kicad_sch, part in row 2, column 2]

Parts:
1V5_MCU1, 2V5_MCU1: TestPoint; TestPoint_Pad_D2.0mm
C50, C51, C52, C55, C56, C57, C58, C59, C61, C62, C63, C66, C67, C68, C70, C71, C72, C73, C75: 0u22; C_0603_1608Metric
C53, C54: 10p; C_0603_1608Metric
C60, C69: 10u; C_1206_3216Metric
C64: 0u047; C_0603_1608Metric
C65: 2u2; C_0603_1608Metric
C74: 1u; C_0603_1608Metric; not fitted
D3, D4, D5, D6, D7, D8: D_Zener_Dual_CommonAnode_AKK; TSOT-23
IC3: S32K344EHT1MPBST; Manufacturer_Part_Number S32K344EHT1MPBST; Mouser Part Number 771-S32K344EHT1MPBST
J1: 8.06.04_J-LINK_NEEDLE_ADAPTER; 80604JLINKNEEDLEADAPTER; Manufacturer_Part_Number 8.06.04 J-LINK NEEDLE ADAPTER
JP8, JP10, JP11, JP12, JP14: Jumper_2_Bridged; PinHeader_1x02_P2.54mm_Vertical
JP9, JP13: Jumper_3_Open; PinHeader_1x03_P2.54mm_Vertical
LED5: HSMG-C170; LEDC2012X80N; Manufacturer_Part_Number HSMG-C170; Mouser Part Number 630-HSMG-C170
Q5: BCP56-10TX; BCP5610TX; Manufacturer_Part_Number BCP56-10TX; Mouser Part Number 771-BCP56-10TX
Q6: BC857BT116; Manufacturer_Part_Number BC857BT116; Mouser Part Number 755-BC857BT116
Q7: BC847BW-7-F; SOT65P210X110-3N; Manufacturer_Part_Number BC847BW-7-F; Mouser Part Number 621-BC847BW-7-F
R64, R83, R85, R86, R87, R90, R91, R92, R105: 10K; R_0603_1608Metric
R65, R66, R67, R68, R69, R70, R71, R73, R74, R75, R76, R77, R78, R79, R80, R81, R82, R93, R94, R96, R97, R99, R102, R103, R106, R109: 0R; SolderJumper-2_P1.3mm_Bridged_Pad1.0x1.5mm
R84, R110: 10K; R_0603_1608Metric; not fitted
R88, R89, R104: 0R; R_0603_1608Metric; not fitted
R95: 150R; R_0603_1608Metric
R98: 4K7; R_0603_1608Metric
R100: 10R; R_0603_1608Metric
R101: 18K; R_0603_1608Metric
R107: 100K; R_0603_1608Metric
R108: 180K; R_0603_1608Metric; not fitted
S2: FSM2JSMAATR; FSM2J_1; Manufacturer_Part_Number FSM2JSMAATR; Mouser Part Number 506-FSM2JSMAATR
V11_MCU1: TestPoint; TestPoint_Pad_D2.0mm
VDD_HV_A_MCU1: TestPoint; TestPoint_Pad_D2.0mm
VDD_HV_A_PERH1: TestPoint; TestPoint_Pad_D2.0mm
VDD_HV_B_MCU2: TestPoint; TestPoint_Pad_D2.0mm
VRC_CTRL_MCU1: TestPoint; TestPoint_Pad_D2.0mm
VREFH1: TestPoint; TestPoint_Pad_D2.0mm
Y1: ECS-160-10-36Q-ES-TR; ECS1601036QESTR; Manufacturer_Part_Number ECS-160-10-36Q-ES-TR; Mouser Part Number 520-160-10-36Q-EST

Connections:
1V5_MCU: 1V5_MCU1.1, C56.1, C57.1, C58.1, C59.1, D3.3 (K), IC3.20 (V15_1), IC3.60 (V15_2), IC3.105 (V15_3), IC3.148 (V15_4), JP9.2 (C)
2V5_MCU: 2V5_MCU1.1, C68.1, D6.3 (K), IC3.19 (V25)
ADC_1: IC3.152 (PTA14)
ADC_2: IC3.7 (PTD1)
CAN0_EN: R106.1
CAN0_ERRN: R66.2
CAN0_RX: R70.2
CAN0_STB: R103.1
CAN0_TX: R69.2
CAN1_EN: R102.1
CAN1_ERRN: R67.2
CAN1_RX: R94.1
CAN1_STB: R99.1
CAN1_TX: R93.1
ENET_INH_PTE12: R73.1
ENET_INT_N: R75.1
ENET_MDC_PTB5: IC3.47 (PTB5)
ENET_MDIO_PTB4: IC3.48 (PTB4)
ENET_MII_RMII_TX_EN: R80.1
ENET_RSTN: R74.1
ENET_RXC_PTD10: R82.1
ENET_RXD0_PTC1: IC3.61 (PTC1)
ENET_RXD1_PTC0: IC3.62 (PTC0)
ENET_RXD2_PTD9: IC3.63 (PTD9)
ENET_RXD3_PTD8: IC3.64 (PTD8)
ENET_RX_DV_PTC17: IC3.65 (PTC17)
ENET_RX_ER_PTC16: IC3.66 (PTC16)
ENET_TXC_PTD11: R81.1
ENET_TXD0_PTC2: R78.1
ENET_TXD1_PTD7: R79.1
ENET_TXD2_PTD6: IC3.53 (PTD5)
ENET_TXD3_PTD5: IC3.52 (PTD6)
EXTAL: C53.1, IC3.23 (EXTAL), Y1.3 (OUT/IN)
FS26_AMUX: R65.1
FS26_VCORE: JP9.1 (A)
GND: C50.2, C51.2, C52.2, C53.2, C54.2, C55.2, C56.2, C57.2, C58.2, C59.2, C60.2, C61.2, C62.2, C63.2, C64.2, C65.2, C66.2, C67.2, C68.2, C69.2, C70.2, C71.2, C72.2, C73.2, C74.2, C75.2, D3.1 (A), D4.1 (A), D5.1 (A), D6.1 (A), D7.1 (A), D8.1 (A), IC3.17 (VREFL), IC3.22 (VSS_1), IC3.24 (VSS_2), IC3.37 (VSS_3), IC3.58 (VSS_4), IC3.78 (VSS_5), IC3.107 (VSS_6), IC3.127 (VSS_7), IC3.150 (VSS_8), IC3.168 (VSS_9), J1.3, J1.5, Q7.2 (E), R90.2, R91.2, R92.2, R107.2, R108.2, R110.2, S2.3, S2.4, Y1.2 (GND_1), Y1.4 (GND_2)
GPIO_0: IC3.123 (PTA3)
GPIO_1: IC3.124 (PTA2)
GPIO_2: IC3.126 (PTB11)
GPIO_3: IC3.131 (PTD26)
GPIO_4: IC3.132 (PTD27)
GPIO_5: IC3.134 (PTD28)
GPIO_6: IC3.135 (PTA1)
GPIO_7: IC3.136 (PTD29)
GPIO_8: IC3.137 (PTA0)
GPIO_9: IC3.138 (PTD30)
JTAG_TCLK/SWD_CLK: IC3.166 (PTC4), J1.4, R84.2, R90.1
JTAG_TDI: IC3.165 (PTC5), J1.8, R86.2
JTAG_TDO: IC3.161 (PTA10), J1.6, R85.2
JTAG_TMS/SWD_DI0: IC3.170 (PTA4), J1.2, R83.2
LIN1_RX: R77.2
LIN1_TX: R76.2
LIN2_RX: R97.1
LIN2_TX: R96.1
unnamed: C52.1, JP9.3 (B), Q5.3 (E), R64.2
unnamed: C54.1, R71.2, Y1.1 (IN/OUT)
unnamed: C64.1, R100.1, S2.1, S2.2
unnamed: IC3.1 (PTA18), R65.2
unnamed: IC3.11 (PTE13), R68.2
unnamed: IC3.29 (PTE12), R73.2
unnamed: IC3.30 (PTA28), R74.2
unnamed: IC3.41 (PTD13), R75.2
unnamed: IC3.50 (PTC2), R78.2
unnamed: IC3.51 (PTD7), R79.2
unnamed: IC3.54 (PTD12), R80.2
unnamed: IC3.55 (PTD11), R81.2
unnamed: IC3.56 (PTD10), R82.2
unnamed: IC3.68 (PTC15), R93.2
unnamed: IC3.71 (PTC14), R94.2
unnamed: IC3.75 (PTB27), R96.2
unnamed: IC3.76 (PTB28), R97.2
unnamed: IC3.81 (PTC13), R99.2
unnamed: IC3.83 (PTC12), R102.2
unnamed: IC3.85 (PTC20), R103.2
unnamed: IC3.86 (PTC21), R106.2
unnamed: IC3.87 (PTC23), R66.1
unnamed: IC3.88 (PTC24), R67.1
unnamed: IC3.100 (PTA7), R69.1
unnamed: IC3.102 (PTA6), R70.1
unnamed: IC3.129 (PTB10), R76.1
unnamed: IC3.130 (PTB9), R77.1
unnamed: IC3.171 (PTA9), R104.1
unnamed: J1.7, R89.1, R91.1
unnamed: J1.9, R88.1, R92.1
unnamed: LED5.1, Q7.3 (C)
unnamed: LED5.2, R95.2
unnamed: Q6.2, R98.2, R101.2
unnamed: Q6.3, R105.1, R107.1
unnamed: Q7.1 (B), R105.2, R108.1, VDD_HV_A_PERH1.1
P3V3_MCU: JP11.2 (B), JP13.3 (B)
P5V0: JP13.1 (A), R95.1
PGOOD_PTA9: R104.2
PTA8: IC3.172 (PTA8)
PTB23: IC3.69 (PTB23)
PTC28: IC3.96 (PTC28)
PTD23: IC3.122 (PTD23)
PTD24: IC3.125 (PTD24)
PTE15: IC3.5 (PTE15)
PTE16: IC3.4 (PTE16)
RESET_MCU: IC3.167 (PTA5), J1.10, R87.2, R100.2, R101.1
SPI_CLK: IC3.98 (PTC8)
SPI_CSB: IC3.95 (PTB0)
SPI_MISO: IC3.97 (PTC9)
SPI_MOSI: IC3.94 (PTB1)
V11_MCU: C65.1, C66.1, C67.1, D5.3 (K), IC3.21 (V11_1), IC3.59 (V11_2), IC3.106 (V11_3), IC3.146 (PTE6), V11_MCU1.1
VDD_HV_A: C55.1, J1.1, JP8.2 (B), JP13.2 (C), JP14.2 (B), R83.1, R84.1, R85.1, R86.1, R87.1, R88.2, R89.2
VDD_HV_A_MCU: C69.1, C70.1, C71.1, C72.1, C73.1, D7.3 (K), IC3.18 (VDD_HV_A_1), IC3.108 (VDD_HV_A_2), IC3.128 (VDD_HV_A_3), IC3.151 (VDD_HV_A_4), IC3.169 (VDD_HV_A_5), JP14.1 (A), R109.1, VDD_HV_A_MCU1.1
VDD_HV_A_PERH: JP8.1 (A), Q6.1, R98.1
VDD_HV_B: JP10.2 (B), JP11.1 (A), JP12.2 (B)
VDD_HV_B_MCU: C50.1, C51.1, C60.1, C61.1, C62.1, C63.1, D4.3 (K), IC3.38 (VDD_HV_B_1), IC3.57 (VDD_HV_B_2), IC3.77 (VDD_HV_B_3), JP12.1 (A), Q5.2 (C_1), Q5.4 (C_2), VDD_HV_B_MCU2.1
VDD_HV_B_PERH: JP10.1 (A)
VRC_CTRL_MCU: Q5.1 (B), R64.1, R68.1, VRC_CTRL_MCU1.1
VREFH: C74.1, C75.1, D8.3 (K), IC3.16 (VREFH), R109.2, R110.1, VREFH1.1
XTAL: IC3.25 (XTAL), R71.1

Notes on the sheet:
-->
DNP
VDD_HV_B_MCU S32K3XX I/Os Supply Voltage Domain
Power Supply Pins
-->
Default closed
1V5 MCU S32K3XX External Supply for V11 Internal Core Logic Voltage Supply
internally regulated
VREFH_MCU SK32K3XX ADC Reference Supply high
LED to indicate when Reset Button was pushed
External NPN Ballast Transistor 1V5
Voltage Selector
VDD_HV_B S32K3XX Secondary I/Os Supply Voltage Domain
1V5 Voltage Selector
VDD_A_PERH
viele freie Pins zur Verfügung
Default 1-2 closed
External Oscillator
VDD_HV_A - Supply Voltage
VDD_HV_A_MCU S32K3XX Primary I/Os Supply Voltage Domain
VDD_B_PERH
1V5 MCU S32K3XX External Supply for V11 Internal Core Logic Voltage Supply
VDD_HV_A S32K3XX Primary I/Os Supply Voltage Domain
<--
FS26 VCORE JP14 1-2 -------------- Ballast Transistor JP14 2-3
VDD_HV_B - Supply Voltage
JTAG
