FabSpi/Zone-Controller/Zonencontroller/power_supply.kicad_sch

## KiCad design Zonencontroller/power_supply.kicad_sch (2025-10-27)

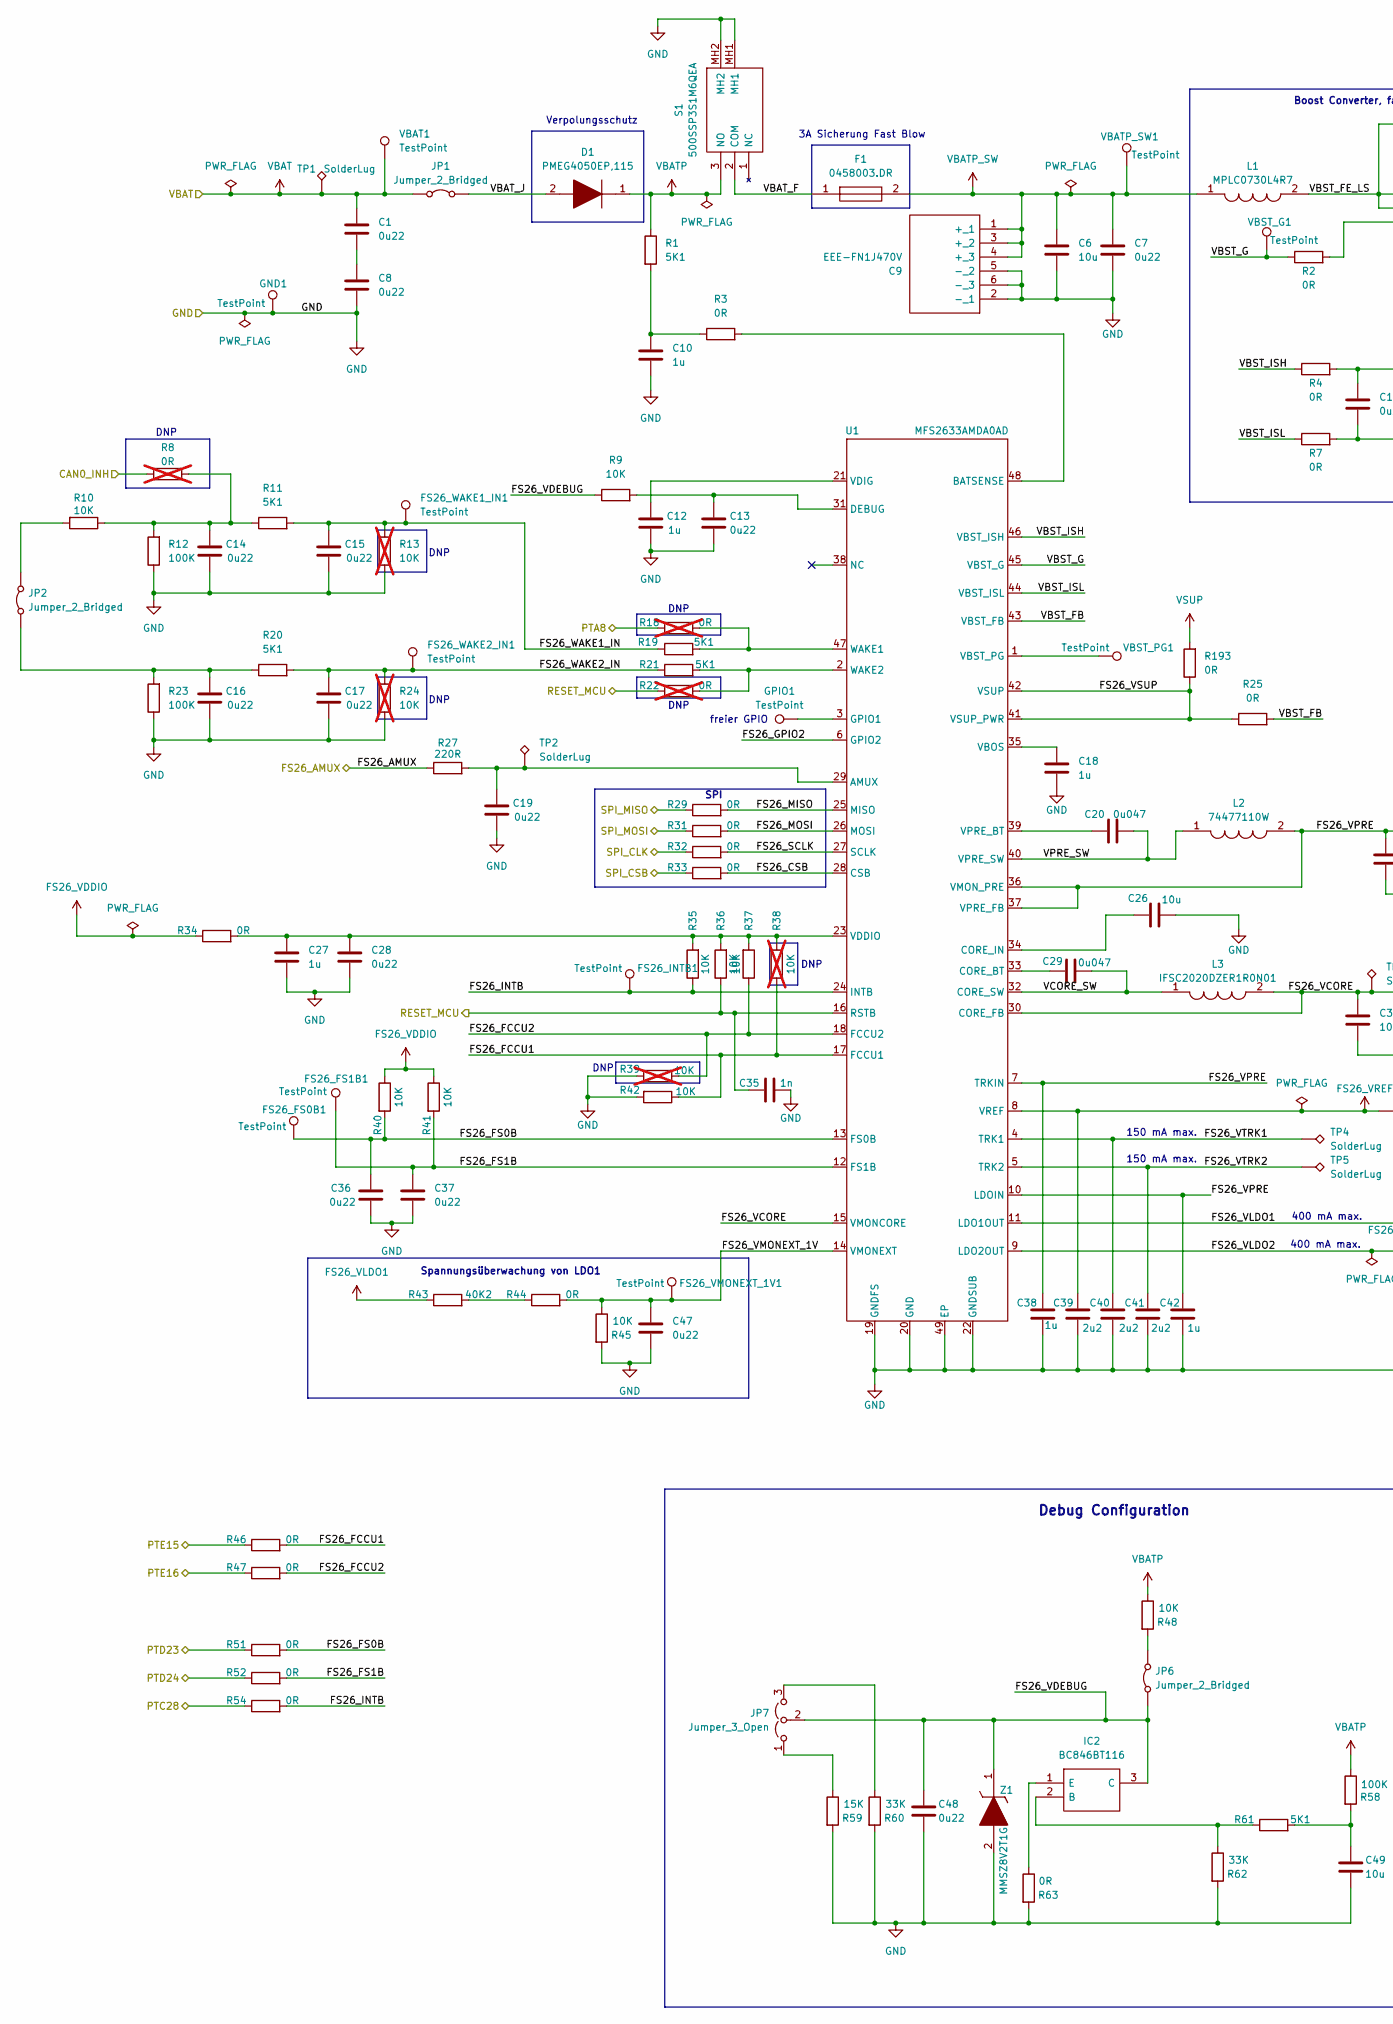
[picture p34: schematic power_supply.kicad_sch, part in row 1, column 1]

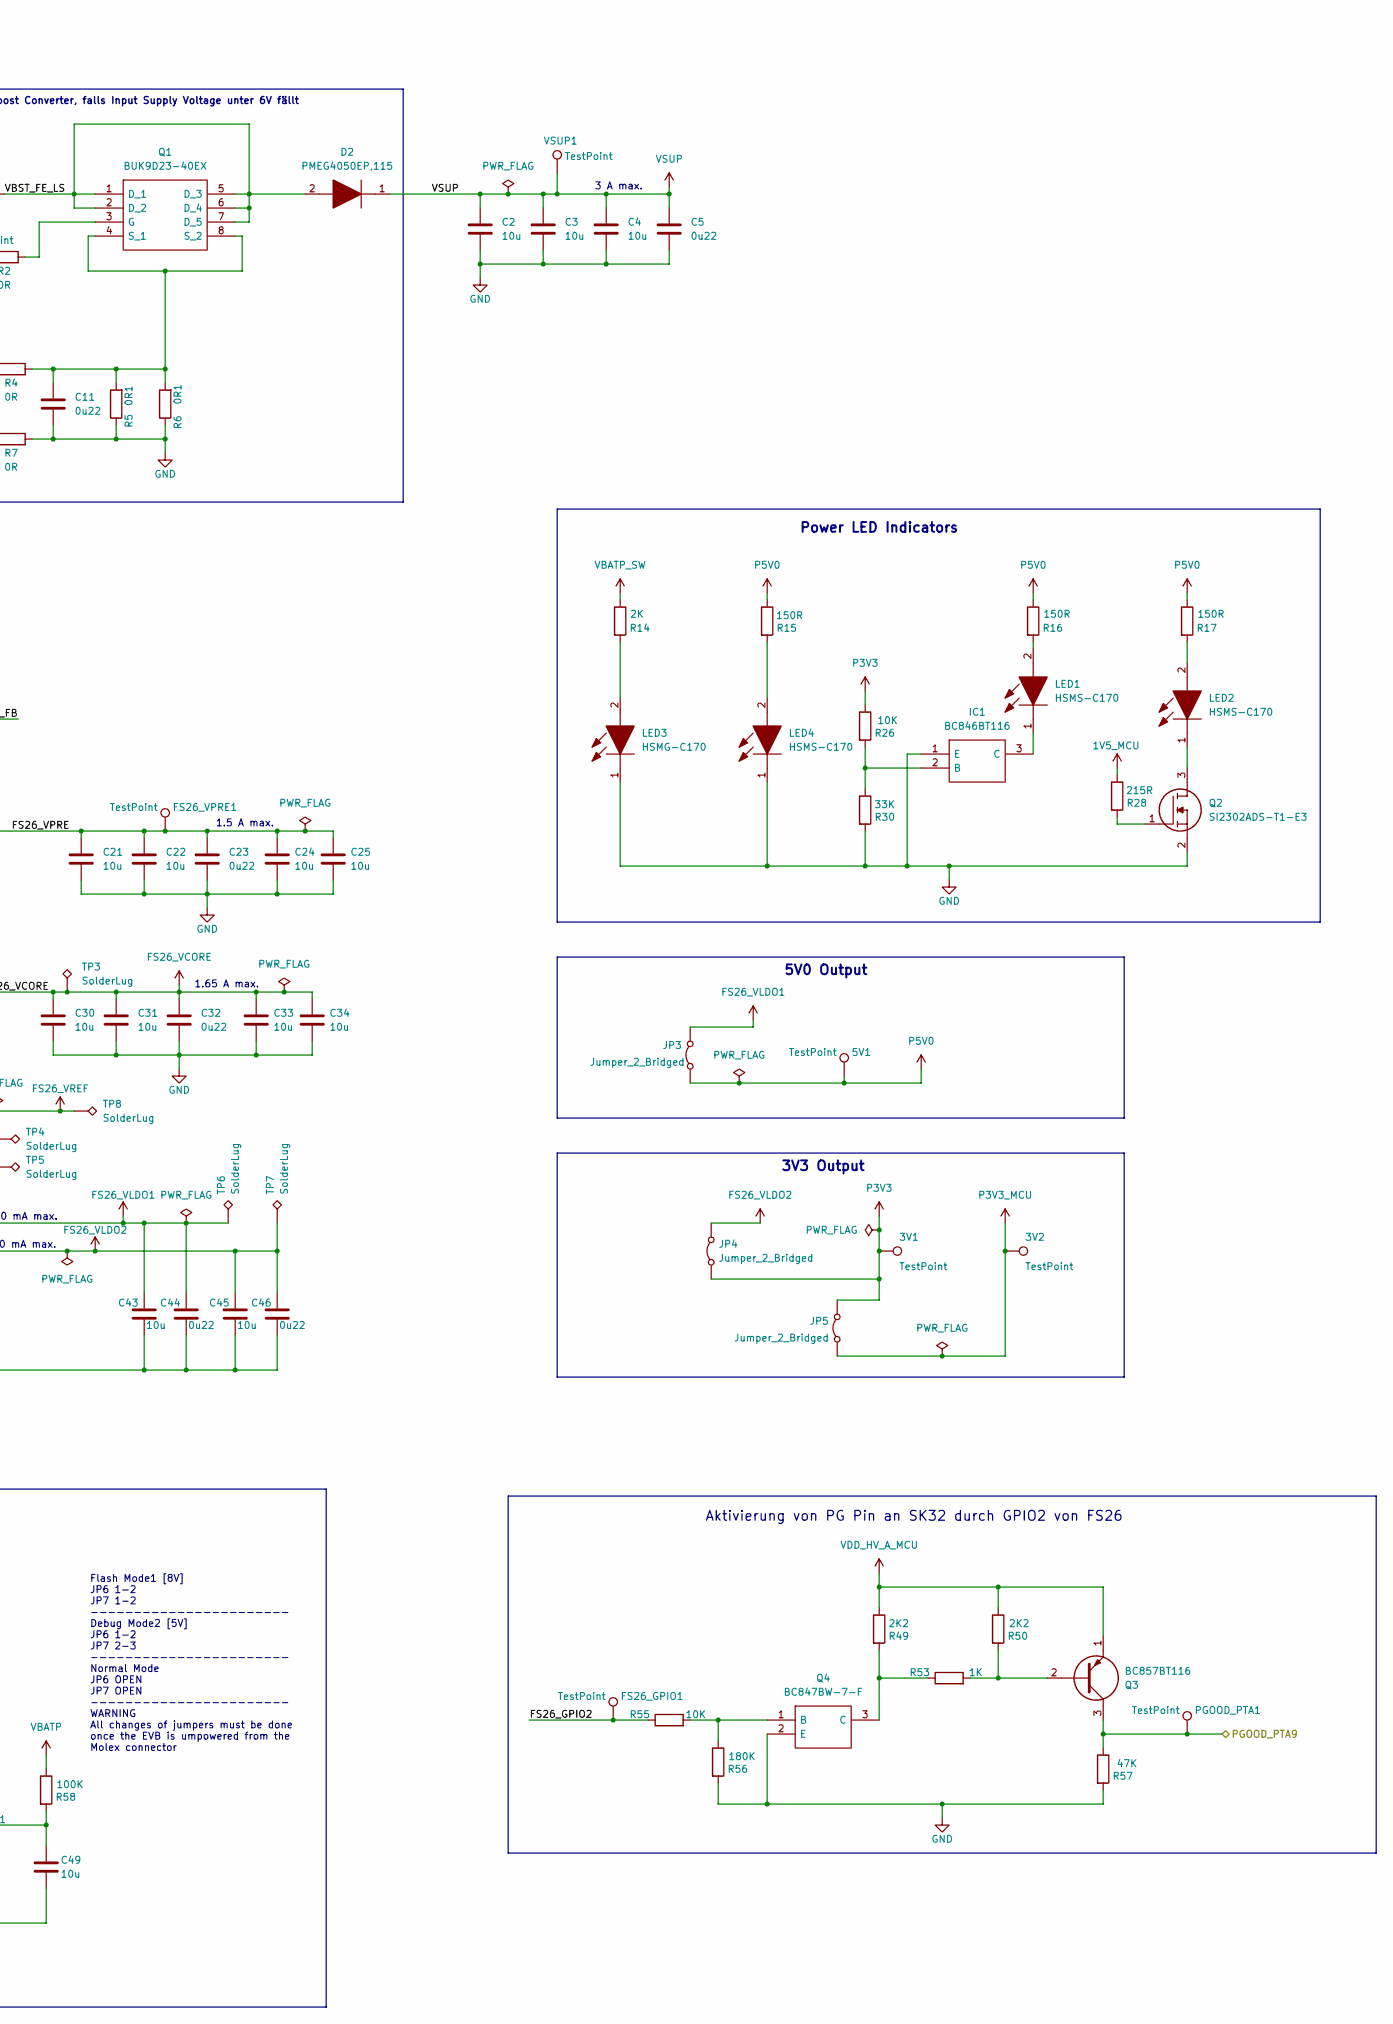
[picture p35: schematic power_supply.kicad_sch, part in row 1, column 2]

Parts:
3V1, 3V2, 5V1: TestPoint; TestPoint_Pad_D2.0mm
C1, C5, C7, C8, C11, C13, C14, C15, C16, C17, C19, C23, C28, C32, C36, C37, C44, C46, C47, C48: 0u22; C_0603_1608Metric
C2, C3, C4, C6, C21, C22, C24, C25, C26, C30, C31, C33, C34, C43, C45, C49: 10u; C_1206_3216Metric
C9: EEE-FN1J470V; EEHZT1E331UV; Manufacturer_Part_Number EEE-FN1J470V; Mouser Part Number 667-EEE-FN1J470V
C10, C12, C18, C27, C38, C42: 1u; C_0603_1608Metric
C20, C29: 0u047; C_0603_1608Metric
C35: 1n; C_0603_1608Metric
C39, C40, C41: 2u2; C_0603_1608Metric
D1, D2: PMEG4050EP,115; SODFL4725X110N; Manufacturer_Part_Number PMEG4050EP,115; Mouser Part Number 771-PMEG4050EP115
F1: 0458003.DR; FUSC3216X158N; Manufacturer_Part_Number 0458003.DR; Mouser Part Number 576-0458003.DR
FS26_FS0B1, FS26_FS1B1, FS26_GPIO1, FS26_INTB1, FS26_VMONEXT_1V1, FS26_VPRE1, FS26_WAKE1_IN1, FS26_WAKE2_IN1: TestPoint; TestPoint_Pad_D2.0mm
GND1: TestPoint; TestPoint_Pad_D2.0mm
GPIO1: TestPoint; TestPoint_Pad_D2.0mm
IC1, IC2: BC846BT116; SOT95P240X120-3N; Manufacturer_Part_Number BC846BT116; Mouser Part Number 755-BC846BT116
JP1, JP2, JP3, JP4, JP5, JP6: Jumper_2_Bridged; PinHeader_1x02_P2.54mm_Vertical
JP7: Jumper_3_Open; PinHeader_1x03_P2.54mm_Vertical
L1: MPLC0730L4R7; Manufacturer_Part_Number MPLC0730L4R7; Mouser Part Number 80-MPLC0730L4R7
L2: 74477110W; INDPM120120X650N; Manufacturer_Part_Number 74477110W; Mouser Part Number 710-74477110W
L3: IFSC2020DZER1R0N01; Manufacturer_Part_Number IFSC2020DZER1R0N01; Mouser Part Number 70-IFSC2020DZR1R0N01
LED1, LED2, LED4: HSMS-C170; LEDC2012X80N; Manufacturer_Part_Number HSMS-C170; Mouser Part Number 630-HSMS-C170
LED3: HSMG-C170; LEDC2012X80N; Manufacturer_Part_Number HSMG-C170; Mouser Part Number 630-HSMG-C170
PGOOD_PTA1: TestPoint; TestPoint_Pad_D2.0mm
Q1: BUK9D23-40EX; BUK9D2340EX; Manufacturer_Part_Number BUK9D23-40EX; Mouser Part Number 771-BUK9D23-40EX
Q2: SI2302ADS-T1-E3; SOT95P237X112-3N; Manufacturer_Part_Number SI2302ADS-T1-E3; Mouser Part Number 781-SI2302ADS-T1-E3
Q3: BC857BT116; Manufacturer_Part_Number BC857BT116; Mouser Part Number 755-BC857BT116
Q4: BC847BW-7-F; SOT65P210X110-3N; Manufacturer_Part_Number BC847BW-7-F; Mouser Part Number 621-BC847BW-7-F
R1, R11, R19, R20, R21, R61: 5K1; R_0603_1608Metric
R2, R3, R4, R7, R25, R29, R31, R32, R33, R34, R44, R46, R47, R51, R52, R54, R63, R193: 0R; SolderJumper-2_P1.3mm_Bridged_Pad1.0x1.5mm
R5, R6: 0R1; R_0603_1608Metric
R8, R18, R22: 0R; R_0603_1608Metric; not fitted
R9, R10, R26, R35, R36, R37, R40, R41, R42, R45, R48, R55: 10K; R_0603_1608Metric
R12, R23, R58: 100K; R_0603_1608Metric
R13, R24, R38, R39: 10K; R_0603_1608Metric; not fitted
R14: 2K; R_0603_1608Metric
R15, R16, R17: 150R; R_0603_1608Metric
R27: 220R; R_0603_1608Metric
R28: 215R; R_0603_1608Metric
R30, R60, R62: 33K; R_0603_1608Metric
R43: 40K2; R_0603_1608Metric
R49, R50: 2K2; R_0603_1608Metric
R53: 1K; R_0603_1608Metric
R56: 180K; R_0603_1608Metric
R57: 47K; R_0603_1608Metric
R59: 15K; R_0603_1608Metric
S1: 500SSP3S1M6QEA; Manufacturer_Part_Number 500SSP3S1M6QEA; Mouser Part Number 612-500SSP3S1M6QEA
TP1, TP2, TP3, TP4, TP5, TP6, TP7, TP8: SolderLug; SolderWire-2sqmm_1x01_D2mm_OD3.9mm
U1: MFS2633AMDA0AD; LQFP-48-1EP_7x7mm_P0.5mm_EP3.6x3.6mm_ThermalVias
VBAT1: TestPoint; TestPoint_Pad_D2.0mm
VBATP_SW1: TestPoint; TestPoint_Pad_D2.0mm
VBST_G1: TestPoint; TestPoint_Pad_D2.0mm
VBST_PG1: TestPoint; TestPoint_Pad_D2.0mm
VSUP1: TestPoint; TestPoint_Pad_D2.0mm
Z1: MMSZ8V2T1G; SOD3716X135N; Manufacturer_Part_Number MMSZ8V2T1G; Mouser Part Number 863-MMSZ8V2T1G

Connections:
1V5_MCU: R28.1
CAN0_INH: R8.2
FS26_AMUX: R27.1
FS26_CSB: R33.2, U1.28 (CSB)
FS26_FCCU1: R38.1, R42.1, R46.2, U1.17 (FCCU1)
FS26_FCCU2: R37.1, R39.1, R47.2, U1.18 (FCCU2)
FS26_FS0B: C36.1, FS26_FS0B1.1, R40.2, R51.2, U1.13 (FS0B)
FS26_FS1B: C37.1, FS26_FS1B1.1, R41.2, R52.2, U1.12 (FS1B)
FS26_GPIO2: FS26_GPIO1.1, R55.1, U1.6 (GPIO2)
FS26_INTB: FS26_INTB1.1, R35.1, R54.2, U1.24 (INTB)
FS26_MISO: R29.2, U1.25 (MISO)
FS26_MOSI: R31.2, U1.26 (MOSI)
FS26_SCLK: R32.2, U1.27 (SCLK)
FS26_VCORE: C30.1, C31.1, C32.1, C33.1, C34.1, L3.2, TP3.1, U1.15 (VMONCORE), U1.30 (CORE_FB)
FS26_VDDIO: R34.1, R40.1, R41.1
FS26_VDEBUG: C48.1, IC2.3 (C), JP6.1 (A), JP7.2 (C), R9.1, Z1.1
FS26_VLDO1: C43.1, C44.1, JP3.2 (B), R43.1, TP6.1, U1.11 (LDO1OUT)
FS26_VLDO2: C45.1, C46.1, JP4.2 (B), TP7.1, U1.9 (LDO2OUT)
FS26_VMONEXT_1V: C47.1, FS26_VMONEXT_1V1.1, R44.2, R45.1, U1.14 (VMONEXT)
FS26_VPRE: C21.1, C22.1, C23.1, C24.1, C25.1, C38.1, C42.1, FS26_VPRE1.1, L2.2, U1.7 (TRKIN), U1.10 (LDOIN), U1.36 (VMON_PRE), U1.37 (VPRE_FB)
FS26_VREF: C39.1, TP8.1, U1.8 (VREF)
FS26_VSUP: R25.1, R193.1, U1.41 (VSUP_PWR), U1.42 (VSUP)
FS26_VTRK1: C40.1, TP4.1, U1.4 (TRK1)
FS26_VTRK2: C41.1, TP5.1, U1.5 (TRK2)
FS26_WAKE1_IN: C15.1, FS26_WAKE1_IN1.1, R11.2, R13.2, R19.1
FS26_WAKE2_IN: C17.1, FS26_WAKE2_IN1.1, R20.2, R21.1, R24.2
GND: C2.2, C3.2, C4.2, C5.2, C6.2, C7.2, C8.2, C9.2 (-_1), C9.5 (-_2), C9.6 (-_3), C10.2, C11.2, C12.2, C13.2, C14.2, C15.2, C16.2, C17.2, C18.2, C19.2, C21.2, C22.2, C23.2, C24.2, C25.2, C26.2, C27.2, C28.2, C30.2, C31.2, C32.2, C33.2, C34.2, C35.2, C36.2, C37.2, C38.2, C39.2, C40.2, C41.2, C42.2, C43.2, C44.2, C45.2, C46.2, C47.2, C48.2, C49.2, GND1.1, IC1.1 (E), LED3.1, LED4.1, Q2.2, Q4.2 (E), R5.1, R6.1, R7.2, R12.1, R13.1, R23.1, R24.1, R30.2, R39.2, R42.2, R45.2, R56.2, R57.2, R59.2, R60.2, R62.2, R63.2, S1.MH1, S1.MH2, U1.19 (GNDFS), U1.20 (GND), U1.22 (GNDSUB), U1.49 (EP), Z1.2
unnamed: C1.2, C8.1
unnamed: C10.1, R1.2, R3.1
unnamed: C11.1, Q1.4 (S_1), Q1.8 (S_2), R4.2, R5.2, R6.2
unnamed: C12.1, U1.21 (VDIG)
unnamed: C13.1, R9.2, U1.31 (DEBUG)
unnamed: C14.1, R8.1, R10.1, R11.1, R12.2
unnamed: C16.1, JP2.1 (A), R20.1, R23.2
unnamed: C18.1, U1.35 (VBOS)
unnamed: C19.1, R27.2, TP2.1, U1.29 (AMUX)
unnamed: C20.1, U1.39 (VPRE_BT)
unnamed: C26.1, U1.34 (CORE_IN)
unnamed: C27.1, C28.1, R34.2, R35.2, R36.2, R37.2, R38.2, U1.23 (VDDIO)
unnamed: C29.1, U1.33 (CORE_BT)
unnamed: C49.1, R58.2, R61.2
unnamed: GPIO1.1, U1.3 (GPIO1)
unnamed: IC1.2 (B), R26.2, R30.1
unnamed: IC1.3 (C), LED1.1
unnamed: IC2.1 (E), R63.1
unnamed: IC2.2 (B), R61.1, R62.1
unnamed: JP2.2 (B), R10.2
unnamed: JP6.2 (B), R48.2
unnamed: JP7.1 (A), R59.1
unnamed: JP7.3 (B), R60.1
unnamed: LED1.2, R16.2
unnamed: LED2.1, Q2.3
unnamed: LED2.2, R17.2
unnamed: LED3.2, R14.2
unnamed: LED4.2, R15.2
unnamed: Q1.3 (G), R2.2
unnamed: Q2.1, R28.2
unnamed: Q3.2, R50.2, R53.2
unnamed: Q4.1 (B), R55.2, R56.1
unnamed: Q4.3 (C), R49.2, R53.1
unnamed: R3.2, U1.48 (BATSENSE)
unnamed: R18.2, R19.2, U1.47 (WAKE1)
unnamed: R21.2, R22.2, U1.2 (WAKE2)
unnamed: R43.2, R44.1
unnamed: U1.1 (VBST_PG), VBST_PG1.1
P3V3: 3V1.1, JP4.1 (A), JP5.2 (B), R26.1
P3V3_MCU: 3V2.1, JP5.1 (A)
P5V0: 5V1.1, JP3.1 (A), R15.1, R16.1, R17.1
PGOOD_PTA9: PGOOD_PTA1.1, Q3.3, R57.1
PTA8: R18.1
PTC28: R54.1
PTD23: R51.1
PTD24: R52.1
PTE15: R46.1
PTE16: R47.1
RESET_MCU: C35.1, R22.1, R36.1, U1.16 (RSTB)
SPI_CLK: R32.1
SPI_CSB: R33.1
SPI_MISO: R29.1
SPI_MOSI: R31.1
VBAT: C1.1, JP1.1 (A), TP1.1, VBAT1.1
VBATP: D1.1, R1.1, R48.1, R58.1, S1.3 (NO)
VBATP_SW: C6.1, C7.1, C9.1 (+_1), C9.3 (+_2), C9.4 (+_3), F1.2, L1.1, R14.1, VBATP_SW1.1
VBAT_F: F1.1, S1.2 (COM)
VBAT_J: D1.2, JP1.2 (B)
VBST_FB: R25.2, U1.43 (VBST_FB)
VBST_FE_LS: D2.2, L1.2, Q1.1 (D_1), Q1.2 (D_2), Q1.5 (D_3), Q1.6 (D_4), Q1.7 (D_5)
VBST_G: R2.1, U1.45 (VBST_G), VBST_G1.1
VBST_ISH: R4.1, U1.46 (VBST_ISH)
VBST_ISL: R7.1, U1.44 (VBST_ISL)
VCORE_SW: C29.2, L3.1, U1.32 (CORE_SW)
VDD_HV_A_MCU: Q3.1, R49.1, R50.1
VPRE_SW: C20.2, L2.1, U1.40 (VPRE_SW)
VSUP: C2.1, C3.1, C4.1, C5.1, D2.1, R193.2, VSUP1.1

Notes on the sheet:
Power LED Indicators
Flash Mode1 [8V] JP6 1-2 JP7 1-2 ----------------------- Debug Mode2 [5V] JP6 1-2 JP7 2-3 ----------------------- Normal Mode JP6 OPEN JP7 OPEN ----------------------- WARNING All changes of jumpers must be done once the EVB is umpowered from the Molex connector
Verpolungsschutz
DNP
150 mA max.
3 A max.
400 mA max.
Aktivierung von PG Pin an SK32 durch GPIO2 von FS26
1.5 A max.
5V0 Output
3A Sicherung Fast Blow
Boost Converter, falls Input Supply Voltage unter 6V fällt
SPI
3V3 Output
1.65 A max.
freier GPIO
Debug Configuration
Spannungsüberwachung von LDO1
